english1234/vstcm/Teensy code/vst_Colour_Mod_v3_stable/vst_Colour_Mod_v3_stable.ino

/*
   VSTCM

   Vector Signal Transceiver Colour Mod using MCP4922 DACs on the Teensy 4.1

   Based on: https://trmm.net/V.st by Trammell Hudson
   incorporating mods made by "Swapfile" (Github) for Advanced Mame compatibility
   and performance optimisations by Fred Cawthorne

   robin@robinchampion.com 2022

*/

#include "main.h"

extern bool should_quit;

void _emu_printf(char *msg) {
  Serial.println(msg);
}

void setup() {
  vstcm_setup();
}

void loop() {
  while (!should_quit)
    mainloop();
}
