english1234/vstcm/Teensy code/vst_Colour_Mod_v3_stable/cinemu.cpp

/*********************************************************
* CINEMU - Cinematronics Emulator / Debugger             *
*                                                        *
* by Zonn Moore 1997                                     *
*                                                        *
* Adapted for Teensy 4.1 / VSTCM colour vector generator *
* Robin Champion September 2022                          *
* robin@robinchampion.com                                *
*                                                        *
**********************************************************/

#include "main.h"

#ifdef VSTCM

#include <arduino.h>
#include <Bounce2.h>
#include <SD.h>

#else

#pragma warning(disable : 4996)  // Get rid of annoying compiler warnings in VC++
#include <cstdio>
#include <cstring>
#include <vcruntime_string.h>
#include <random>
#include SDL_PATH

#endif

#include "cinemu.h"
#include "drawing.h"

#ifdef VSTCM
// Bounce objects to read five pushbuttons (pins 0-4)
static Bounce button0 = Bounce();
static Bounce button1 = Bounce();
static Bounce button2 = Bounce();
static Bounce button3 = Bounce();
static Bounce button4 = Bounce();

extern void SPI_flush();
#else
extern SDL_Renderer *rend_2D_orig;  // Renderer for original 2D game
#endif

UINT8 *rom;  // Allocated as 0x8000 by a malloc
extern char gMsg[50];

/* Simple public domain implementation of the standard CRC32 checksum.
 * Outputs the checksum for each file given as a command line argument.
 * Invalid file names and files that cause errors are silently skipped.
 * The program reads from stdin if it is called with no arguments. */

uint32_t crc32_for_byte(uint32_t r) {
  for (int j = 0; j < 8; ++j)
    r = (r & 1 ? 0 : (uint32_t)0xEDB88320L) ^ r >> 1;
  return r ^ (uint32_t)0xFF000000L;
}

uint32_t crc32(const void *data, size_t n_bytes, uint32_t *crc) {
  static uint32_t table[0x100];
  if (!*table)
    for (size_t i = 0; i < 0x100; ++i)
      table[i] = crc32_for_byte(i);

  for (size_t i = 0; i < n_bytes; ++i)
    *crc = table[(uint8_t)*crc ^ ((uint8_t *)data)[i]] ^ *crc >> 8;
  return *crc;
}

int loadROM(const char *fn, unsigned char *block, const unsigned len) {
#ifdef VSTCM
  unsigned j;

  // open the file on the sd card
  File dataFile = SD.open(fn, FILE_READ);

  if (dataFile) {
    //Serial.println(fn);

    for (j = 0; j < len; j++)
      block[j] = dataFile.read();

    // close the file:
    dataFile.close();

    return 0;
  }

  // if the file didn't open, print an error:
  //Serial.print("Error opening file: ");
  //Serial.println(fn);
#else
  char rompath[100];
  strcpy(rompath, MY_ROMPATH);
  strcat(rompath, fn);

  FILE *f = fopen(rompath, "rb");
  if (f == NULL) {
    strcpy(gMsg, "error: can't open file");
    fprintf(stderr, "error: can't open file '%s'.\n", rompath);
    return 1;
  }

  size_t result = fread(block, sizeof(uint8_t), len, f);
  if (result != len) {
    strcpy(gMsg, "error: while reading file");
    fprintf(stderr, "error: while reading file '%s'\n", rompath);
    return 1;
  }

  fclose(f);
  return 0;
#endif
  return -1;
}

/**************************** main **********************************/
int Game;

#define No 0
#define Yes 1

bool loadTailgunner() {
  //Serial.println("loadTailgunner: starting");
  unsigned char romLoad[0x2000];
  int r = 0;
  r += loadROM("roms/tailg/tgunner.t70", &romLoad[0x0000], 0x800);
  r += loadROM("roms/tailg/tgunner.p70", &romLoad[0x0800], 0x800);
  r += loadROM("roms/tailg/tgunner.t71", &romLoad[0x1000], 0x800);
  r += loadROM("roms/tailg/tgunner.p71", &romLoad[0x1800], 0x800);
  uint32_t crc;

  crc = 0;
  if (crc32(&romLoad[0x0000], 0x800, &crc) != 0x21EC9A04) r -= 1;
  crc = 0;
  if (crc32(&romLoad[0x0800], 0x800, &crc) != 0x8D7410B3) r -= 1;
  crc = 0;
  if (crc32(&romLoad[0x1000], 0x800, &crc) != 0x2C954AB6) r -= 1;
  crc = 0;
  if (crc32(&romLoad[0x1800], 0x800, &crc) != 0x8E2C8494) r -= 1;

  for (int i = 0; i < 0x800; i++) {
    rom[i * 2] = romLoad[0x0000 + i];
    rom[1 + i * 2] = romLoad[0x0800 + i];
    rom[0x1000 + i * 2] = romLoad[0x1000 + 0x0000 + i];
    rom[0x1000 + 1 + i * 2] = romLoad[0x1000 + 0x0800 + i];
  }

  if (r != 0) {
    strcpy(gMsg, "TROUBLE WITH TAIL GUNNER ROMS!");
    //Serial.println("TROUBLE WITH TAIL GUNNER ROMS!");
    return false;
  }

  return true;
}

bool loadRipoff() {
  unsigned char romLoad[0x2000];
  int r = 0;
  r += loadROM("roms/ripoff/ripoff.t7", &romLoad[0x0000], 0x800);
  r += loadROM("roms/ripoff/ripoff.p7", &romLoad[0x0800], 0x800);
  r += loadROM("roms/ripoff/ripoff.u7", &romLoad[0x1000], 0x800);
  r += loadROM("roms/ripoff/ripoff.r7", &romLoad[0x1800], 0x800);
  uint32_t crc;

  crc = 0;
  if (crc32(&romLoad[0x0000], 0x800, &crc) != 0x40C2C5B8) r -= 1;
  crc = 0;
  if (crc32(&romLoad[0x0800], 0x800, &crc) != 0xA9208AFB) r -= 1;
  crc = 0;
  if (crc32(&romLoad[0x1000], 0x800, &crc) != 0x29C13701) r -= 1;
  crc = 0;
  if (crc32(&romLoad[0x1800], 0x800, &crc) != 0x150BD4C8) r -= 1;

  for (int i = 0; i < 0x800; i++) {
    rom[i * 2] = romLoad[0x0000 + i];
    rom[1 + i * 2] = romLoad[0x0800 + i];
    rom[0x1000 + i * 2] = romLoad[0x1000 + 0x0000 + i];
    rom[0x1000 + 1 + i * 2] = romLoad[0x1000 + 0x0800 + i];
  }

  if (r != 0) {
    strcpy(gMsg, "TROUBLE WITH RIP OFF ROMS!");
    //Serial.println("TROUBLE WITH RIP OFF ROMS!");
    return false;
  }

  return true;
}

bool loadArmorAttack() {
  unsigned char romLoad[0x4000];
  int r = 0;
  r += loadROM("roms/armora/ar414le.t6", &romLoad[0x0000], 0x800);
  r += loadROM("roms/armora/ar414lo.p6", &romLoad[0x1000], 0x800);
  r += loadROM("roms/armora/ar414ue.u6", &romLoad[0x2000], 0x800);
  r += loadROM("roms/armora/ar414uo.r6", &romLoad[0x3000], 0x800);
  uint32_t crc;

  crc = 0;
  if (crc32(&romLoad[0x0000], 0x1000, &crc) != 0xD7E71F84) r -= 1;
  crc = 0;
  if (crc32(&romLoad[0x1000], 0x1000, &crc) != 0xDF1C2370) r -= 1;
  crc = 0;
  if (crc32(&romLoad[0x2000], 0x1000, &crc) != 0xB0276118) r -= 1;
  crc = 0;
  if (crc32(&romLoad[0x3000], 0x1000, &crc) != 0x229D779F) r -= 1;

  for (int i = 0; i < 0x1000; i++) {
    rom[i * 2] = romLoad[0x0000 + i];
    rom[1 + i * 2] = romLoad[0x1000 + i];
    rom[0x2000 + i * 2] = romLoad[0x2000 + 0x0000 + i];
    rom[0x2000 + 1 + i * 2] = romLoad[0x2000 + 0x1000 + i];
  }

  if (r != 0) {
    strcpy(gMsg, "TROUBLE WITH ARMOR ATTACK ROMS!");
    //Serial.println("TROUBLE WITH ARMOR ATTACK ROMS!");
    return false;
  }

  return true;
}

bool loadDemon() {
  unsigned char romLoad[0x4000];
  int r = 0;
  r += loadROM("roms/demon/demon.7t", &romLoad[0x0000], 0x800);
  r += loadROM("roms/demon/demon.7p", &romLoad[0x1000], 0x800);
  r += loadROM("roms/demon/demon.7u", &romLoad[0x2000], 0x800);
  r += loadROM("roms/demon/demon.7r", &romLoad[0x3000], 0x800);
  uint32_t crc;

  crc = 0;
  if (crc32(&romLoad[0x0000], 0x1000, &crc) != 0x866596C1) r -= 1;
  crc = 0;
  if (crc32(&romLoad[0x1000], 0x1000, &crc) != 0x1109E2F1) r -= 1;
  crc = 0;
  if (crc32(&romLoad[0x2000], 0x1000, &crc) != 0xD447A3C3) r -= 1;
  crc = 0;
  if (crc32(&romLoad[0x3000], 0x1000, &crc) != 0x64B515F0) r -= 1;

  for (int i = 0; i < 0x1000; i++) {
    rom[i * 2] = romLoad[0x0000 + i];
    rom[1 + i * 2] = romLoad[0x1000 + i];
    rom[0x2000 + i * 2] = romLoad[0x2000 + 0x0000 + i];
    rom[0x2000 + 1 + i * 2] = romLoad[0x2000 + 0x1000 + i];
  }

  if (r != 0) {
    strcpy(gMsg, "TROUBLE WITH DEMON ROMS!");
    //Serial.println("TROUBLE WITH DEMON ROMS!");
    return false;
  }

  return true;
}

bool loadSolarQuest() {
  unsigned char romLoad[0x4000];
  int r = 0;
  uint32_t crc;

  r += loadROM("roms/solarq/solar.6t", &romLoad[0x0000], 0x800);
  r += loadROM("roms/solarq/solar.6p", &romLoad[0x1000], 0x800);
  r += loadROM("roms/solarq/solar.6u", &romLoad[0x2000], 0x800);
  r += loadROM("roms/solarq/solar.6r", &romLoad[0x3000], 0x800);
  if (r == 0) {

  } else {
    r = 0;
    r += loadROM("roms/solarq/sq-2_le.6t", &romLoad[0x0000], 0x1000);
    r += loadROM("roms/solarq/sq-2_lo.6p", &romLoad[0x1000], 0x1000);
    r += loadROM("roms/solarq/sq-2_ue.6u", &romLoad[0x2000], 0x1000);
    r += loadROM("roms/solarq/sq-2_uo.6r", &romLoad[0x3000], 0x1000);
  }

  crc = 0;
  if (crc32(&romLoad[0x0000], 0x1000, &crc) != 0x1F3C5333) r -= 1;
  crc = 0;
  if (crc32(&romLoad[0x1000], 0x1000, &crc) != 0xD6C16BCC) r -= 1;
  crc = 0;
  if (crc32(&romLoad[0x2000], 0x1000, &crc) != 0xA5970E5C) r -= 1;
  crc = 0;
  if (crc32(&romLoad[0x3000], 0x1000, &crc) != 0xB763FFF2) r -= 1;

  for (int i = 0; i < 0x1000; i++) {
    rom[i * 2] = romLoad[0x0000 + i];
    rom[1 + i * 2] = romLoad[0x1000 + i];
    rom[0x2000 + i * 2] = romLoad[0x2000 + 0x0000 + i];
    rom[0x2000 + 1 + i * 2] = romLoad[0x2000 + 0x1000 + i];
  }

  if (r != 0) {
    strcpy(gMsg, "TROUBLE WITH SOLAR QUEST ROMS!");
    //Serial.println("TROUBLE WITH SOLAR QUEST ROMS!");
    return false;
  }

  return true;
}

bool loadWotw() {
  unsigned char romLoad[0x4000];
  int r = 0;
  r += loadROM("roms/wotw/wow_le.t7", &romLoad[0x0000], 0x1000);
  r += loadROM("roms/wotw/wow_lo.p7", &romLoad[0x1000], 0x1000);
  r += loadROM("roms/wotw/wow_ue.u7", &romLoad[0x2000], 0x1000);
  r += loadROM("roms/wotw/wow_uo.r7", &romLoad[0x3000], 0x1000);
  uint32_t crc;

  crc = 0;
  if (crc32(&romLoad[0x0000], 0x1000, &crc) != 0xB16440F9) r -= 1;
  crc = 0;
  if (crc32(&romLoad[0x1000], 0x1000, &crc) != 0xBFDF4A5A) r -= 1;
  crc = 0;
  if (crc32(&romLoad[0x2000], 0x1000, &crc) != 0x9B5CEA48) r -= 1;
  crc = 0;
  if (crc32(&romLoad[0x3000], 0x1000, &crc) != 0xC9D3C866) r -= 1;

  for (int i = 0; i < 0x1000; i++) {
    rom[i * 2] = romLoad[0x0000 + i];
    rom[1 + i * 2] = romLoad[0x1000 + i];
    rom[0x2000 + i * 2] = romLoad[0x2000 + 0x0000 + i];
    rom[0x2000 + 1 + i * 2] = romLoad[0x2000 + 0x1000 + i];
  }

  if (r != 0) {
    strcpy(gMsg, "TROUBLE WITH WAR OF THE WORLDS ROMS!");
    //Serial.println("TROUBLE WITH WAR OF THE WORLDS ROMS!");
    return false;
  }

  return true;
}

bool loadStarCastle() {
  unsigned char romLoad[0x4000];
  int r = 0;
  r += loadROM("roms/starcas/starcas3.t7", &romLoad[0x0000], 0x0800);
  r += loadROM("roms/starcas/starcas3.p7", &romLoad[0x0800], 0x0800);
  r += loadROM("roms/starcas/starcas3.u7", &romLoad[0x1000], 0x0800);
  r += loadROM("roms/starcas/starcas3.r7", &romLoad[0x1800], 0x0800);
  uint32_t crc;

  crc = 0;
  if (crc32(&romLoad[0x0000], 0x0800, &crc) != 0xB5838B5D) r -= 1;
  crc = 0;
  if (crc32(&romLoad[0x0800], 0x0800, &crc) != 0xF6BC2F4D) r -= 1;
  crc = 0;
  if (crc32(&romLoad[0x1000], 0x0800, &crc) != 0x188CD97C) r -= 1;
  crc = 0;
  if (crc32(&romLoad[0x1800], 0x0800, &crc) != 0xC367B69D) r -= 1;

  for (int i = 0; i < 0x0800; i++) {
    rom[i * 2] = romLoad[0x0000 + i];
    rom[1 + i * 2] = romLoad[0x0800 + i];
    rom[0x1000 + i * 2] = romLoad[0x1000 + 0x0000 + i];
    rom[0x1000 + 1 + i * 2] = romLoad[0x1000 + 0x0800 + i];
  }

  if (r != 0) {
    strcpy(gMsg, "TROUBLE WITH STAR CASTLE ROMS!");
    //Serial.println("TROUBLE WITH STAR CASTLE ROMS!");
    return false;
  }

  return true;
}

bool loadSpeedFreak() {
  unsigned char romLoad[0x4000];
  int r = 0;
  r += loadROM("roms/speedfrk/speedfrk.t7", &romLoad[0x0000], 0x0800);
  r += loadROM("roms/speedfrk/speedfrk.p7", &romLoad[0x0800], 0x0800);
  r += loadROM("roms/speedfrk/speedfrk.u7", &romLoad[0x1000], 0x0800);
  r += loadROM("roms/speedfrk/speedfrk.r7", &romLoad[0x1800], 0x0800);
  uint32_t crc;

  crc = 0;
  if (crc32(&romLoad[0x0000], 0x0800, &crc) != 0x3552C03F) r -= 1;
  crc = 0;
  if (crc32(&romLoad[0x0800], 0x0800, &crc) != 0x4B90CDEC) r -= 1;
  crc = 0;
  if (crc32(&romLoad[0x1000], 0x0800, &crc) != 0x616C7CF9) r -= 1;
  crc = 0;
  if (crc32(&romLoad[0x1800], 0x0800, &crc) != 0xFBE90D63) r -= 1;

  for (int i = 0; i < 0x0800; i++) {
    rom[i * 2] = romLoad[0x0000 + i];
    rom[1 + i * 2] = romLoad[0x0800 + i];
    rom[0x1000 + i * 2] = romLoad[0x1000 + 0x0000 + i];
    rom[0x1000 + 1 + i * 2] = romLoad[0x1000 + 0x0800 + i];
  }

  if (r != 0) {
    strcpy(gMsg, "TROUBLE WITH SPEED FREAK ROMS!");
    //Serial.println("TROUBLE WITH SPEED FREAK ROMS!");
    return false;
  }

  return true;
}

bool loadWarrior() {
  unsigned char romLoad[0x4000];
  int r = 0;
  r += loadROM("roms/warrior/warrior.t7", &romLoad[0x0000], 0x0800);
  r += loadROM("roms/warrior/warrior.p7", &romLoad[0x0800], 0x0800);
  r += loadROM("roms/warrior/warrior.u7", &romLoad[0x1000], 0x0800);
  r += loadROM("roms/warrior/warrior.r7", &romLoad[0x1800], 0x0800);
  uint32_t crc;

  crc = 0;
  if (crc32(&romLoad[0x0000], 0x0800, &crc) != 0xAC3646F9) r -= 1;
  crc = 0;
  if (crc32(&romLoad[0x0800], 0x0800, &crc) != 0x517D3021) r -= 1;
  crc = 0;
  if (crc32(&romLoad[0x1000], 0x0800, &crc) != 0x2E39340F) r -= 1;
  crc = 0;
  if (crc32(&romLoad[0x1800], 0x0800, &crc) != 0x8E91B502) r -= 1;

  for (int i = 0; i < 0x0800; i++) {
    rom[i * 2] = romLoad[0x0000 + i];
    rom[1 + i * 2] = romLoad[0x0800 + i];
    rom[0x1000 + i * 2] = romLoad[0x1000 + 0x0000 + i];
    rom[0x1000 + 1 + i * 2] = romLoad[0x1000 + 0x0800 + i];
  }

  if (r != 0) {
    strcpy(gMsg, "TROUBLE WITH WARRIOR ROMS!");
    //Serial.println("TROUBLE WITH WARRIOR ROMS!");
    return false;
  }

  return true;
}

bool loadSundance() {
  unsigned char romLoad[0x4000];
  int r = 0;
  r += loadROM("roms/sundance/sundance.t7", &romLoad[0x0000], 0x0800);
  r += loadROM("roms/sundance/sundance.p7", &romLoad[0x0800], 0x0800);
  r += loadROM("roms/sundance/sundance.u7", &romLoad[0x1000], 0x0800);
  r += loadROM("roms/sundance/sundance.r7", &romLoad[0x1800], 0x0800);
  uint32_t crc;

  crc = 0;
  if (crc32(&romLoad[0x0000], 0x0800, &crc) != 0xD5B9CB19) r -= 1;
  crc = 0;
  if (crc32(&romLoad[0x0800], 0x0800, &crc) != 0x445C4F20) r -= 1;
  crc = 0;
  if (crc32(&romLoad[0x1000], 0x0800, &crc) != 0x67887D48) r -= 1;
  crc = 0;
  if (crc32(&romLoad[0x1800], 0x0800, &crc) != 0x10B77EBD) r -= 1;

  for (int i = 0; i < 0x0800; i++) {
    rom[i * 2] = romLoad[0x0000 + i];
    rom[1 + i * 2] = romLoad[0x0800 + i];
    rom[0x1000 + i * 2] = romLoad[0x1000 + 0x0000 + i];
    rom[0x1000 + 1 + i * 2] = romLoad[0x1000 + 0x0800 + i];
  }

  if (r != 0) {
    strcpy(gMsg, "TROUBLE WITH SUNDANCE ROMS!");
    //Serial.println("TROUBLE WITH SUNDANCE ROMS!");
    return false;
  }

  return true;
}

bool loadSpaceWar() {
  unsigned char romLoad[0x2000];
  int r = 0;
  r += loadROM("roms/spacewar/spacewar.1l", &romLoad[0x0000], 0x0800);
  r += loadROM("roms/spacewar/spacewar.2r", &romLoad[0x0800], 0x0800);
  uint32_t crc;

  crc = 0;
  if (crc32(&romLoad[0x0000], 0x800, &crc) != 0xEDF0FD53) r -= 1;
  crc = 0;
  if (crc32(&romLoad[0x0800], 0x800, &crc) != 0x4F21328B) r -= 1;

  for (int i = 0; i < 0x800; i++) {
    rom[i * 2] = romLoad[0x0000 + i];
    rom[1 + i * 2] = romLoad[0x0800 + i];
  }


  if (r != 0) {
    strcpy(gMsg, "TROUBLE WITH SPACE WARS ROMS!");
    //Serial.println("TROUBLE WITH SPACE WARS ROMS!");
    return false;
  }

  return true;
}

bool loadStarHawk() {
  unsigned char romLoad[0x2000];
  int r = 0;
  r += loadROM("roms/starhawk/u7", &romLoad[0x0000], 0x0800);
  r += loadROM("roms/starhawk/r7", &romLoad[0x0800], 0x0800);
  uint32_t crc;
  crc = 0;

  crc = 0;
  if (crc32(&romLoad[0x0000], 0x800, &crc) != 0x376E6C5C) r -= 1;
  crc = 0;
  if (crc32(&romLoad[0x0800], 0x800, &crc) != 0xBB71144F) r -= 1;

  for (int i = 0; i < 0x800; i++) {
    rom[i * 2] = romLoad[0x0000 + i];
    rom[1 + i * 2] = romLoad[0x0800 + i];
  }

  if (r != 0) {
    strcpy(gMsg, "TROUBLE WITH STAR HAWK ROMS!");
    //Serial.println("TROUBLE WITH STAR HAWK ROMS!");
    return false;
  }

  return true;
}

bool loadBarrier() {
  unsigned char romLoad[0x2000];
  int r = 0;
  r += loadROM("roms/barrier/barrier.t7", &romLoad[0x0000], 0x0800);
  r += loadROM("roms/barrier/barrier.p7", &romLoad[0x0800], 0x0800);
  uint32_t crc;
  crc = 0;

  crc = 0;
  if (crc32(&romLoad[0x0000], 0x800, &crc) != 0x7C3D68C8) r -= 1;
  crc = 0;
  if (crc32(&romLoad[0x0800], 0x800, &crc) != 0xAEC142B5) r -= 1;

  for (int i = 0; i < 0x800; i++) {
    rom[i * 2] = romLoad[0x0000 + i];
    rom[1 + i * 2] = romLoad[0x0800 + i];
  }

  if (r != 0) {
    strcpy(gMsg, "TROUBLE WITH BARRIER ROMS!");
    //Serial.println("TROUBLE WITH BARRIER ROMS!");
    return false;
  }

  return true;
}

bool loadBoxingBugs() {
  unsigned char romLoad[0x8000];
  int r = 0;
  r += loadROM("roms/boxingb/u1a", &romLoad[0x0000], 0x1000);
  r += loadROM("roms/boxingb/u1b", &romLoad[0x1000], 0x1000);
  r += loadROM("roms/boxingb/u2a", &romLoad[0x2000], 0x1000);
  r += loadROM("roms/boxingb/u2b", &romLoad[0x3000], 0x1000);
  r += loadROM("roms/boxingb/u3a", &romLoad[0x4000], 0x1000);
  r += loadROM("roms/boxingb/u3b", &romLoad[0x5000], 0x1000);
  r += loadROM("roms/boxingb/u4a", &romLoad[0x6000], 0x1000);
  r += loadROM("roms/boxingb/u4b", &romLoad[0x7000], 0x1000);
  uint32_t crc;

  crc = 0;
  if (crc32(&romLoad[0x0000], 0x1000, &crc) != 0xD3115B0F) r -= 1;
  crc = 0;
  if (crc32(&romLoad[0x1000], 0x1000, &crc) != 0x3A44268D) r -= 1;
  crc = 0;
  if (crc32(&romLoad[0x2000], 0x1000, &crc) != 0xC97A9CBB) r -= 1;
  crc = 0;
  if (crc32(&romLoad[0x3000], 0x1000, &crc) != 0x98D34FF5) r -= 1;
  crc = 0;
  if (crc32(&romLoad[0x4000], 0x1000, &crc) != 0x5BB3269B) r -= 1;
  crc = 0;
  if (crc32(&romLoad[0x5000], 0x1000, &crc) != 0x85BF83AD) r -= 1;
  crc = 0;
  if (crc32(&romLoad[0x6000], 0x1000, &crc) != 0x25B51799) r -= 1;
  crc = 0;
  if (crc32(&romLoad[0x7000], 0x1000, &crc) != 0x7F41DE6A) r -= 1;

  for (int i = 0; i < 0x1000; i++) {
    rom[i * 2] = romLoad[0x0000 + i];
    rom[1 + i * 2] = romLoad[0x1000 + i];
    rom[0x2000 + i * 2] = romLoad[0x2000 + 0x0000 + i];
    rom[0x2000 + 1 + i * 2] = romLoad[0x2000 + 0x1000 + i];
    rom[0x4000 + i * 2] = romLoad[0x4000 + 0x0000 + i];
    rom[0x4000 + 1 + i * 2] = romLoad[0x4000 + 0x1000 + i];
    rom[0x6000 + i * 2] = romLoad[0x6000 + 0x0000 + i];
    rom[0x6000 + 1 + i * 2] = romLoad[0x6000 + 0x1000 + i];
  }

  if (r != 0) {
    strcpy(gMsg, "TROUBLE WITH BOXING BUGS ROMS!");
    //Serial.println("TROUBLE WITH BOXING BUGS ROMS!");
    return false;
  }

  return true;
}

bool loadCosmicChasm() {
  int r = 1;
  // this seems to be a 64k ROM
  // - or I don't know how to load it...

  // MAME roms contain u1 - u16 (each 4k)
  /*
   * 
   * Is there a bankswitch
   * Or do they use the full 64kk address space?
     RomImages[0]="roms/cosmicchasm/chasm.u4";
     RomImages[1]="roms/cosmicchasm/chasm.u12";
     RomImages[2]="roms/cosmicchasm/chasm.u8";
     RomImages[3]="roms/cosmicchasm/chasm.u16";
     RomImages[4]="roms/cosmicchasm/chasm.u3";
     RomImages[5]="roms/cosmicchasm/chasm.u11";
     RomImages[6]="roms/cosmicchasm/chasm.u7";
     RomImages[7]="roms/cosmicchasm/chasm.u15";
     
     what about 1 / 9
     what about 2 / 10
     what about 5 / 13
     what about 6 / 14
     ???
     
     INFO: MAME
     MCFG_CPU_ADD("maincpu", M68000, CCHASM_68K_CLOCK)    / * 8 MHz (from schematics) * /
     
ROM_START( cchasm )
    ROM_REGION( 0x010000, "maincpu", 0 )
    ROM_LOAD16_BYTE( "chasm.u4",  0x000000, 0x001000, CRC(19244f25) SHA1(79deaae82da8d1b16d05bbac43ba900c4b1d9f26) )
    ROM_LOAD16_BYTE( "chasm.u12", 0x000001, 0x001000, CRC(5d702c7d) SHA1(cbdceed45a1112594fbcbeb6976edc932b32d518) )
    ROM_LOAD16_BYTE( "chasm.u8",  0x002000, 0x001000, CRC(56a7ce8a) SHA1(14c790dcddb78d3b81b5a65fe3529e42c9708273) )
    ROM_LOAD16_BYTE( "chasm.u16", 0x002001, 0x001000, CRC(2e192db0) SHA1(1a8ff983295ab52b5099c089b3142cdc56d28aee) )
    ROM_LOAD16_BYTE( "chasm.u3",  0x004000, 0x001000, CRC(9c71c600) SHA1(900526eaff7483fc478ebfb3f14796ff8fd1d01f) )
    ROM_LOAD16_BYTE( "chasm.u11", 0x004001, 0x001000, CRC(a4eb59a5) SHA1(a7bb3ca8f1f000f224def6342ca9d1eabcb210e6) )
    ROM_LOAD16_BYTE( "chasm.u7",  0x006000, 0x001000, CRC(8308dd6e) SHA1(82ad7c27e9a41af5280ecd975d3530ff2ed27ad4) )
    ROM_LOAD16_BYTE( "chasm.u15", 0x006001, 0x001000, CRC(9d3abf97) SHA1(476d684182d92d66263df82e1b5c4ff24b6814e8) )
    ROM_LOAD16_BYTE( "u2",        0x008000, 0x001000, CRC(4e076ae7) SHA1(a72f5425b256785b810ee5f23917b44f778cfcd3) )
    ROM_LOAD16_BYTE( "u10",       0x008001, 0x001000, CRC(cc9e19ca) SHA1(6c46ec265c2cc0683470ed1df978b96b577c5ca1) )
    ROM_LOAD16_BYTE( "chasm.u6",  0x00a000, 0x001000, CRC(a96525d2) SHA1(1c41bc3bf051cf1830182cbde6fba4e56db7e431) )
    ROM_LOAD16_BYTE( "chasm.u14", 0x00a001, 0x001000, CRC(8e426628) SHA1(2d70a7717b18cc892332b9d5d2de3ceba6c1481d) )
    ROM_LOAD16_BYTE( "u1",        0x00c000, 0x001000, CRC(88b71027) SHA1(49fa676d7838c643d642fbc70579ce29e76ba724) )
    ROM_LOAD16_BYTE( "chasm.u9",  0x00c001, 0x001000, CRC(d90c9773) SHA1(4033f0579f0782db2157f6cbece53b0d74e61d4f) )
    ROM_LOAD16_BYTE( "chasm.u5",  0x00e000, 0x001000, CRC(e4a58b7d) SHA1(0e5f948cd110804e6119fafb4e3fa5904dd1390f) )
    ROM_LOAD16_BYTE( "chasm.u13", 0x00e001, 0x001000, CRC(877e849c) SHA1(bdeb97fcb7488e7f0866dd651204c362d2ec9f4f) )

    ROM_REGION( 0x10000, "audiocpu", 0 )
    ROM_LOAD( "2732.bin", 0x0000, 0x1000, CRC(715adc4a) SHA1(426be4f3334ef7f2e8eb4d533e64276c30812aa3) )

    ROM_REGION( 0x0200, "plds", 0 )
    ROM_LOAD( "pal12l6.u76", 0x0000, 0x0034, CRC(a30e02b7) SHA1(572f6d3f03e559f12e3bd5e087d7680ac69e9182) )
    ROM_LOAD( "pal12l6.u77", 0x0100, 0x0034, CRC(458b9cdb) SHA1(a3bff56d805f6dc494d294f079c3580430acf317) )
ROM_END     
     
     */
  if (r != 0) {
    strcpy(gMsg, "TROUBLE WITH COSMIC CHASM ROMS!");
    //Serial.println("TROUBLE WITH COSMIC CHASM ROMS!");
    return false;
  }

  return true;
}

bool loadQB3() {
  unsigned char romLoad[0x8000];
  int r = 0;

  r += loadROM("roms/qb3/qb3_le_t7.bin", &romLoad[0x0000], 0x2000);
  r += loadROM("roms/qb3/qb3_lo_p7.bin", &romLoad[0x2000], 0x2000);
  r += loadROM("roms/qb3/qb3_ue_u7.bin", &romLoad[0x4000], 0x2000);
  r += loadROM("roms/qb3/qb3_uo_r7.bin", &romLoad[0x6000], 0x2000);

  uint32_t crc;

  crc = 0;
  if (crc32(&romLoad[0x0000], 0x2000, &crc) != 0xADAAEE4C) r -= 1;
  crc = 0;
  if (crc32(&romLoad[0x2000], 0x2000, &crc) != 0x72F6199F) r -= 1;
  crc = 0;
  if (crc32(&romLoad[0x4000], 0x2000, &crc) != 0x050A996D) r -= 1;
  crc = 0;
  if (crc32(&romLoad[0x6000], 0x2000, &crc) != 0x33FA77A2) r -= 1;

  for (int i = 0; i < 0x2000; i++) {
    rom[i * 2] = romLoad[0x0000 + i];
    rom[1 + i * 2] = romLoad[0x2000 + i];
    rom[0x4000 + i * 2] = romLoad[0x4000 + 0x0000 + i];
    rom[0x4000 + 1 + i * 2] = romLoad[0x4000 + 0x2000 + i];
  }

  if (r != 0) {
    strcpy(gMsg, "TROUBLE WITH QB3 ROMS!");
    //Serial.println("TROUBLE WITH QB3 ROMS!");
    return false;
  }

  return true;
}

// these should be in the vectrex library
#define VEC_BUTTON_1_1 0x01
#define VEC_BUTTON_1_2 0x02
#define VEC_BUTTON_1_3 0x04
#define VEC_BUTTON_1_4 0x08
#define VEC_BUTTON_2_1 0x10
#define VEC_BUTTON_2_2 0x20
#define VEC_BUTTON_2_3 0x40
#define VEC_BUTTON_2_4 0x80

// Put any switch or IO bits that are common to all machines here.
#define SW_ABORT 0x100 /* for ioSwitches */

int useParity = 0;

static int world_xl = -1800, world_yb = -2400, world_xr = 1800, world_yt = 2400;  // dummy values should never be used

unsigned long isqrt(unsigned long x) {
  unsigned long op, res, one;

  op = x;
  res = 0;

  /* "one" starts at the highest power of four <= than the argument. */
  one = 1 << 30; /* second-to-top bit set */
  while (one > op) one >>= 2;

  while (one != 0) {
    if (op >= res + one) {
      op -= res + one;
      res += one << 1;  // <-- faster than 2 * one
    }
    res >>= 1;
    one >>= 2;
  }
  return res;
}

const int /*fp14*/ sine[] = {
  0,
  402,
  803,
  1205,
  1605,
  2005,
  2404,
  2801,
  3196,
  3589,
  3980,
  4369,
  4756,
  5139,
  5519,
  5896,
  6269,
  6639,
  7005,
  7366,
  7723,
  8075,
  8423,
  8765,
  9102,
  9434,
  9759,
  10079,
  10393,
  10701,
  11002,
  11297,
  11585,
  11866,
  12139,
  12406,
  12665,
  12916,
  13159,
  13395,
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
};

FILE *debugf = NULL;

#define DEBUG_OUT(a, b) \
  Serial.print(a); \
  Serial.print(" "); \
  Serial.println(b);

/*#ifndef false
#define false (0 != 0)
#define true (0 == 0)
#endif*/

// Start of CCPU emulator

int ccpudebug = 0; /* default is off (0) - can be turned on with -d flag */

// war of the worlds had a missing instruction.  Now added and it runs.

/*
boxingbugs had a missing instruction:

2EAE: C8    : ldi  $8     : A=047 B=045 I=047Z J=E9B P=1 A0=46 00 N1 O46 A
2EAF: EA    : lda  [i]    : A=18D B=045 I=047Z J=E9B P=1 A0=47 00 N18D O47 AA
2EB0: D7    : sta  $7     : A=18D B=045 I=017Z J=E9B P=1 A0=47 00 N18D O47 A
2EB1: 02    : lda  #$200  : A=200 B=045 I=017Z J=E9B P=1 A0=8D 01 N200 O18D AA
2EB2: 76    : sub  $6     : A=13C B=045 I=016Z J=E9B P=1 A0=00 11 NC4 O200 AA
2EB3: 57    : nopb        : A=13C B=045 I=016Z J=E9B P=1 A0=00 11 NC4 O200   B
2EB4: 03    : lda  #$300  : A=13C B=300 I=016Z J=E9B P=1 A0=3C 01 N300 O45 AA
2EB5: 57    : nopb        : A=13C B=300 I=016Z J=E9B P=1 A0=3C 01 N300 O45   B
2eb6 DANGER: Unimplemented instruction - opLSRe B 1
 */

/*

Had to add missing opcode to get cosmicchasm to run - now it runs but is
stuck in a loop:

0840: 30 39 : sub  #$39   : A=040 B=039 I=08CZ J=840 P=8 A0=40 10 N39 O72 AA
0842: 00    : clr         : A=000 B=039 I=08CZ J=840 P=8 A0=40 00 N0 O40 AA
0843: FF    : lsld        : A=000 B=072 I=08CZ J=840 P=8 A0=00 0F NFFF O0 AA
0844: EA    : lda  [i]    : A=000 B=072 I=08CZ J=840 P=8 A0=00 00 N0 O0 AA
0845: 90    : out  $0     : A=000 B=072 I=08CZ J=840 P=8 A0=00 00 N0 O0 A
0846: E3    : mul  [i]    : A=000 B=039 I=08CZ J=840 P=8 A0=00 00 N0 O0 AA
0847: 40 48 : ldj  #$840  : A=000 B=039 I=08CZ J=840 P=8 A0=00 00 N0 O0 A
0849: C0    : ldi  $0     : A=000 B=039 I=000Z J=840 P=8 A0=00 00 N0 O0 A
084A: D0    : sta  $0     : A=000 B=039 I=080Z J=840 P=8 A0=00 00 N0 O0 A
084B: BC    : cmp  $C     : A=000 B=039 I=08CZ J=840 P=8 A0=00 10 N0 O0 AA
084C: 00    : clr         : A=000 B=039 I=08CZ J=840 P=8 A0=00 00 N0 O0 AA
084D: FF    : lsld        : A=000 B=072 I=08CZ J=840 P=8 A0=00 0F NFFF O0 AA
084E: EB    : lsr         : A=000 B=072 I=08CZ J=840 P=8 A0=00 0B NBEB O0 AA
084F: 88    : ldp  #$8    : A=000 B=072 I=08CZ J=840 P=8 A0=00 0B NBEB O0 A
0850: 20 40 : add  #$40   : A=040 B=072 I=08CZ J=840 P=8 A0=00 00 N40 O0 AA
0852: 52    : jdrb <jump> : A=040 B=072 I=08CZ J=840 P=8 A0=00 00 N40 O0   B
0852: 52    : jdrb <jump> : A=040 B=072 I=08CZ J=840 P=8 A0=00 00 N40 O0   BB
0853: 50    : jppb <jump> : A=040 B=072 I=08CZ J=840 P=8 A0=00 00 N40 O0   B

*/
#define CARRYBIT (1 << 12)
#define A0BIT 1

/* Contorted sign-extend macro only evaluates its parameter once, and
   executes in two shifts.  This is far more efficient that any other
   sign extend procedure I can think of, and relatively safe */

#define SEX(twelvebit) ((((int)twelvebit) << (int)((sizeof(int) * 8) - 12)) \
                        >> (int)((sizeof(int) * 8) - 12))

/* Mouse values currently sampled once per frame and set in WAI code.
   This is not ideal. */

/* RCstate setting macros to exit opcode handler */
#define jumpCineRet_A \
  do { \
    RCstate = RCstate_A; \
    goto cineExecBottom; \
  } while (0)
#define jumpCineRet_B \
  do { \
    RCstate = RCstate_B; \
    goto cineExecBottom; \
  } while (0)
#define jumpCineRet_AA \
  do { \
    RCstate = RCstate_AA; \
    goto cineExecBottom; \
  } while (0)
#define jumpCineRet_BB \
  do { \
    RCstate = RCstate_BB; \
    goto cineExecBottom; \
  } while (0)
#define jumpCineRet_WEIRD \
  do (DEBUG_OUT( "Didn't bother yet.\n" ); exit ( 0 ); \
  } \
  while (0)

/* Handy new operators ... */

/* for Zonn translation :) */
#define SAR16(var, arg) (((signed short int)var) >> arg)

/* for setting/checking the A0 flag */
#define SETA0(var) (RCacc_a0 = var)
#define GETA0() (RCacc_a0)

/* for setting/checking the Carry flag */
#define SETFC(val) (RCflag_C = val)
#define GETFC() ((RCflag_C >> 8) & 0xFF)

/* Define new types for the c-cpu emulator */
typedef short unsigned int RCCINEWORD; /* 12bits on the C-CPU */
typedef unsigned char RCCINEBYTE;      /* 8 (or less) bits on the C-CPU */
typedef short signed int RCCINESWORD;  /* 12bits on the C-CPU */
typedef signed char RCCINESBYTE;       /* 8 (or less) bits on the C-CPU */

typedef enum {
  RCstate_A = 0,
  RCstate_AA,
  RCstate_B,
  RCstate_BB
} RCCINESTATE; /* current RCstate */

volatile static UINT32 dwElapsedTicks = 0;
static UINT8 bBailOut = false;

/* C-CPU context information begins -- */
RCCINEWORD RCregister_PC = 0; /* C-CPU registers; program counter */
RCCINEWORD RCregister_A = 0;  /* ; A-Register (accumulator) */
RCCINEWORD RCregister_B = 0;  /* ; B-Register (accumulator) */
RCCINEBYTE RCregister_I = 0;  /* ; I-Register (last access RAM location) */
RCCINEWORD RCregister_J = 0;  /* ; J-Register (target address for JMP
				   opcodes) */
RCCINEBYTE RCregister_P = 0;  /* ; Page-Register (4 bits) */
RCCINEWORD RCFromX = 0;       /* ; X-Register (start of a vector) */
RCCINEWORD RCFromY = 0;       /* ; Y-Register (start of a vector) */
RCCINEWORD RCregister_T = 0;  /* ; T-Register (vector draw length timer) */
RCCINEWORD RCflag_C = 0;      /* C-CPU flags; carry. Is word sized, instead
				   of RCCINEBYTE, so we can do direct
				   assignment and then change to BYTE during
				   inspection. */

RCCINEWORD RCcmp_old = 0; /* last accumulator value */
RCCINEWORD RCcmp_new = 0; /* new accumulator value */
RCCINEBYTE RCacc_a0 = 0;  /* bit0 of A-reg at last accumulator access */

RCCINESTATE RCstate = RCstate_A; /* C-CPU RCstate machine current
					   RCstate */
RCCINEWORD RCram[256];           /* C-CPU RCram (for all pages) */

//UINT8 rom[0x8000];  // = tailgunner was 0x2000 - others may be larger

static char ccpu_game_name[32]; /* canonical name we now use as cinemu
				   parameter */
static int ccpu_game_id = 0;    /* as set by cineSetGame */
static UINT8 ccpu_jmi_dip = 1;  /* as set by cineSetJMI */
static UINT8 ccpu_msize = 0;    /* as set by cineSetMSize */
static UINT8 ccpu_monitor = 0;  /* as set by cineSetMonitor */

/* cinem graphics junk */
RCCINEBYTE RCvgShiftLength = 0; /* number of shifts loaded into length reg */

/* -- Context information ends. */

UINT8 bFlipX;
UINT8 bFlipY;
UINT8 bSwapXY;
UINT8 bOverlay;

UINT16 ioSwitches = 0xFF;      /* high values for non-triggered switches */
UINT16 initialSwitches = 0xFF; /* high values for non-triggered switches */
UINT16 ioInputs = 0;
UINT16 initialInputs = 0;
UINT8 ioOutputs = 0;

UINT16 RCvgColour = 0;

INT16 JoyX;
INT16 JoyY;
UINT8 bNewFrame;

INT32 sdwGameXSize;
INT32 sdwGameYSize;
INT32 sdwXOffset = 0;
INT32 sdwYOffset = 0;

// This will move to the vectrex graphics library.
static int64_t ScaleXMul = 1LL, ScaleXDiv = 1LL, ScaleXOffsetPre = 0LL, ScaleXOffsetPost = 0LL,
               ScaleYMul = 1LL, ScaleYDiv = 1LL, ScaleYOffsetPre = 0LL, ScaleYOffsetPost = 0LL;
static int v_rotate = 0, v_flip_x = 0, v_flip_y = 0;
static int v_xl = 0, v_yb = 0, v_xr = 0, v_yt = 0;

int tx(int x) {  // convert x from window to viewport
  if (v_flip_x) x = v_xr - (x - v_xl);
  return (int)(((((int64_t)x) + ScaleXOffsetPre) * ScaleXMul) / ScaleXDiv + ScaleXOffsetPost);
}

int ty(int y) {  // and y
  if (v_flip_y) y = v_yt - (y - v_yb);
  return (int)(((((int64_t)y) + ScaleYOffsetPre) * ScaleYMul) / ScaleYDiv + ScaleYOffsetPost);
}

int frameCounter = 0;
static int cineTwinkle = 255;  // off by default

void line(int32_t xl, int32_t yb, int32_t xr, int32_t yt, int col) {

  /*  Serial.print("xl ");
  Serial.print(xl);
  Serial.print(" yb ");
  Serial.print(yb);
  Serial.print(" xr ");
  Serial.print(xr);
  Serial.print(" yt ");
  Serial.print(yt);
  Serial.print(" col ");
  Serial.println(col);
*/
  if (v_rotate) {
    int tmp;
    tmp = xl;
    xl = yb;
    yb = tmp;
    tmp = xr;
    xr = yt;
    yt = tmp;
    xl = v_xr - (xl - v_xl);
    xr = v_xr - (xr - v_xl);
  }

  cohen_sutherlandCustom(&xl, &yb, &xr, &yt, 128, 128, 3968, 3968);

  if (xl == 1000000)  // if not totally outside defined clipping region then draw it
    return;

  if ((ccpu_game_id == GAME_TAILGUNNER) && (xl == xr) && (yb == yt)) {
    // stars...  tweak the intensity according to the distance from the center
    int SCREEN_W = world_xr - world_xl, SCREEN_H = world_yt - world_yb;
    int dist = isqrt((SCREEN_W / 2 - xl) * (SCREEN_W / 2 - xl) + (SCREEN_H / 2 - yb) * (SCREEN_H / 2 - yb));
    int maxdist = isqrt((SCREEN_W / 2) * (SCREEN_W / 2) + (SCREEN_H / 2) * (SCREEN_H / 2));

    if (maxdist == 0)
      maxdist = 1;

    if (col == 7)
      col = (col - (((maxdist - dist) * 7) / maxdist) + 1) * 2 + 1;

    //v_directDraw32Patterned(tx(xl), ty(yb), tx(xr), ty(yt), (col + 1) * 8 - 1, random());
    //  col = (col + 1) * 8 - 1;
    // col = random(30, 160);

    draw_moveto(tx(xl), ty(yb));
    draw_to_xyrgb(tx(xr), ty(yt), col, col, col);
  } else if ((ccpu_game_id == GAME_TAILGUNNER) && (RCregister_PC == 0x03B2)) {
    // 0x1BBD - PUSH START
    // 0x03B2 - 3 lines in the shields have Twinkle values
    // Tailgunner's shields are funny and need fixing.
    //v_directDraw32Patterned(tx(xl), ty(yb), tx(xr), ty(yt), 127, random());  //one way to make sparky shields...
    //  col = random(30, 160);
    draw_moveto(tx(xl), ty(yb));
    draw_to_xyrgb(tx(xr), ty(yt), col, col, col);
    //DEBUG_OUT("line(%d,%d, %d,%d, %02x) at PC=0x%04x;\n", xl,yb, xr,yt, col, RCregister_PC);
  } else {  // All other games except Tailgunner
    /* Twinkle may be 0 (sundance), or 7-9 */
    if ((col <= cineTwinkle) || (xl != xr) || (yb != yt)) {
      // DEBUG_OUT("v_directDraw32 (%d,%d, %d,%d, %d);\n", tx(xl), ty(yb), tx(xr), ty(yt), (col + 1) * 8 - 1);
      // v_directDraw32(tx(xl), ty(yb), tx(xr), ty(yt), (col + 1) * 8 - 1);
      col = (col + 1) * 10 - 1;

    } else {  // twinkle parameter denotes flash.
      col = (127 * (sine[(frameCounter << 3) & 255] + 16384 + 32768)) / 65536;
      //  v_directDraw32(tx(xl), ty(yb), tx(xr), ty(yt), col);  // brightness 63..127
    }

    draw_moveto(tx(xl), ty(yb));
    draw_to_xyrgb(tx(xr), ty(yt), col, col, col);
  }
}

int _tx(int x) {  // convert x from window to viewport
  if (v_flip_x) x = v_xr - (x - v_xl);
  return (int)(((((int64_t)x) + ScaleXOffsetPre) * ScaleXMul) / ScaleXDiv + ScaleXOffsetPost);
}

int _ty(int y) {  // and y
  if (v_flip_y) y = v_yt - (y - v_yb);
  return (int)(((((int64_t)y) + ScaleYOffsetPre) * ScaleYMul) / ScaleYDiv + ScaleYOffsetPost);
}

void window(int xl, int yb, int xr, int yt) {
  // We will use normalised viewport coordinates of x = -18000:18000 and y = -24000:24000 for consistency
  int64_t width, height;
  int xc, yc;
  int /* oxl = xl, oyb = yb, */ oxr = xr, oyt = yt;

  v_xl = xl;
  v_yb = yb;
  v_xr = xr;
  v_yt = yt;

  width = (int64_t)xr - (int64_t)xl;
  height = (int64_t)yt - (int64_t)yb;
  // However, if OS tells us that vectrex is on its side, we'll handle these differently.
  // For now, though, Malban's orientation code is doing the rotation behind the scenes
  // so we don't want to do it twice.  Need to think about whether that solution is OK
  // or has to be changed. Although it doesn't matter too much in terms of what is displayed,
  // it makes a different with respect to loading and saving configs and using the same
  // default for multiple games.
  if (width * 4 > height * 3) {
    // window is wider than aspect ratio, so we will have black bars at the top and bottom
    // height = (width * 4) / 3;
    yc = (yb + yt) / 2;
    yb = yc - height / 2;
    yt = yc + height / 2;
  } else if (width * 4 < height * 3) {
    // window is taller than aspect ratio, so we will have black bars at
    // the sides
    width = (height * 3) / 4;
    xc = (xl + xr) / 2;
    xl = xc - width / 2;
    xr = xc + width / 2;
  }

  ScaleXMul = 4096LL;
  ScaleXDiv = width;
  // ScaleXOffsetPre = -width / 2LL;
  ScaleXOffsetPre = 0;
  ScaleXOffsetPost = 0LL;
  ScaleXOffsetPost = (tx(xr) - tx(oxr)) / 2LL;

  ScaleYMul = 4096LL;
  ScaleYDiv = height;
  // ScaleYOffsetPre = -height / 2LL;
  ScaleYOffsetPre = 0;
  ScaleYOffsetPost = 0LL;
  ScaleYOffsetPost = (ty(yt) - ty(oyt)) / 2LL;
}
// end of window library

// start of startFrame section

void startFrame_ripoff(void) {
  /*
DIP_START(ripoff_dips)
 DIP_SET4(DIPSW1,0xfc,"Units",0x00,"8",0x01,"16",0x02,"4",0x03,"12",3)
 DIP_SET4(DIPSW1,0xf3,"Coins",0x08,"2Coins 1Credit",0x00,"4Coins 3Credits",0x0c,"1Coin 1Credit",0x04,"2Coins 3Credits",2)
 DIP_SET2(DIPSW1,0xef,"Attract Sound",0x10,"Off",0x00,"On",0)
 DIP_SET2(DIPSW1,0xdf,"Scores",0x20,"Individual",0x00,"Combined",0)
 DIP_SET2(DIPSW1,0xbf,"Diagnostic",0x00,"Off",0x40,"On",0)
DIP_END
   */
#define RO_IO_P1START 0x02  // 1-player start
#define RO_IO_P1LEFT 0x1000
#define RO_IO_P1RIGHT 0x4000
#define RO_IO_P1THRUST 0x8000
#define RO_IO_P1FIRE 0x2000

#define RO_IO_P2START 0x08  // 2-player start
#define RO_IO_P2LEFT 0x01
#define RO_IO_P2RIGHT 0x04
#define RO_IO_P2THRUST 0x10
#define RO_IO_P2FIRE 0x20

#define RO_SW_ABORT SW_ABORT /* for ioSwitches */
#define RO_SW_COIN 0x080

  // static int prevButtonState = 0;  // for debouncing

  frameCounter += 1;
  // DEBUG_OUT("// Frame %d\n", frameCounter);

  // v_WaitRecal();
  // v_doSound();
  // v_readButtons();  // update currentButtonState
  // v_readJoystick1Analog();
  //v_readJoystick2Analog ();  // Apparently we are getting joystick 2 data anyway?????
  // v_playAllSFX();

  // Unfortunately, it's quite common to press LEFT and RIGHT simultaneously by accident with this
  // layout, and accidentally invoke the configuration screen.  Need to think about how we will
  // handle this...

  // default inactive:
  ioInputs = initialInputs | RO_IO_P1LEFT | RO_IO_P1RIGHT | RO_IO_P1THRUST | RO_IO_P1FIRE | RO_IO_P1START | RO_IO_P2LEFT | RO_IO_P2RIGHT | RO_IO_P2THRUST | RO_IO_P2FIRE | RO_IO_P2START;
  ioSwitches = initialSwitches | RO_SW_COIN;

  // digital joysticks...
  // commented out to get it to compile
  /* if (currentJoy1X < -30) ioInputs &= ~RO_IO_P1LEFT;
   if (currentJoy1X > 30) ioInputs &= ~RO_IO_P1RIGHT;
   if (currentJoy1Y > 30) ioInputs &= ~RO_IO_P1THRUST;

   if (currentJoy2X < -30) ioInputs &= ~RO_IO_P2LEFT;
   if (currentJoy2X > 30) ioInputs &= ~RO_IO_P2RIGHT;
   if (currentJoy2Y > 30) ioInputs &= ~RO_IO_P2THRUST;

   // would be helpful to examine ram and make these context-dependent

   if ((currentButtonState & ~prevButtonState) & (VEC_BUTTON_1_1 | VEC_BUTTON_2_1)) ioSwitches &= ~RO_SW_COIN;	// only on rising edge */


  // if (currentButtonState & VEC_BUTTON_1_2) ioInputs &= ~RO_IO_P1START; // needs 1 coin
#ifdef VSTCM
  // Update the button objects
  button2.update();
  // middle button on PCB starts game
  if (button2.fell()) {
    ioSwitches &= ~RO_SW_COIN;
    ioInputs &= ~RO_IO_P1START;  // needs 1 coin
  }
#endif
  /* if (currentButtonState & VEC_BUTTON_2_2) ioInputs &= ~RO_IO_P2START; // needs 2 coins and second controller

   if (currentButtonState & VEC_BUTTON_1_1) ioInputs &= ~RO_IO_P1LEFT;
   if (currentButtonState & VEC_BUTTON_1_2) ioInputs &= ~RO_IO_P1RIGHT;
   if (currentButtonState & VEC_BUTTON_1_3) ioInputs &= ~RO_IO_P1THRUST;
   if (currentButtonState & VEC_BUTTON_1_4) ioInputs &= ~RO_IO_P1FIRE;

   if (currentButtonState & VEC_BUTTON_2_1) ioInputs &= ~RO_IO_P2LEFT;
   if (currentButtonState & VEC_BUTTON_2_2) ioInputs &= ~RO_IO_P2RIGHT;
   if (currentButtonState & VEC_BUTTON_2_3) ioInputs &= ~RO_IO_P2THRUST;
   if (currentButtonState & VEC_BUTTON_2_4) ioInputs &= ~RO_IO_P2FIRE;
   prevButtonState = currentButtonState;
*/
#ifdef NEVER
  /*
# Initialization file for Rip Off (Single Player)
>
>*** Rip Off (Single Player) ***
>
>Keyboard Mapping:
>
>   One Player  = F1
>   Two Players = F2
>   Coin        = F3
>   Reset Game  = F4
>   Exit        = <Esc>
>
>   Left        = 'Z'
>   Right       = 'X'
>   Thrust      = '.'
>   Fire        = '/'

 ; Switch definitions:
 ;
 ;   D------  0=Normal, 1=Diagnostics
 ;   -O-----  0=Individual Scores, 1=Combined Scores
 ;   --S----  0=Sound in attract mode, 1=No Sound (sound not supported)
 ;
 ;   ---CC--  11 = 1 credit per 1 quarter
 ;            10 = 1 credit per 2 quarters
 ;            01 = 3 credits per 2 quarters
 ;            00 = 3 credits per 4 quarters
 ;
 ;   -----TT  11 = 12 fuel pods
 ;            10 = 4 fuel pods
 ;            00 = 8 fuel pods
 ;            01 = 16 fuel pods

 Switches=0011101

[Inputs]
 RstCPU  = 02000000,FFFFFFFF,00000000,FFFFFFFF	; Set bit indicating RESET
 Exit    = 01000000,FFFFFFFF,00000000,FFFFFFFF	; Set bit indicating Exit 
 Coin    = 00000000,FFFFFFFF,00000000,FF7FFFFF

 Player1 = 00000000,FFFFFFFD,00000002,FFFFFFFF
 Player2 = 00000000,FFFFFFF7,00000008,FFFFFFFF

 RFire   = 00000000,FFFFDFFF,00002000,FFFFFFFF
 RThrust = 00000000,FFFF7FFF,00008000,FFFFFFFF
 RRight  = 00000000,FFFFBFFF,00004000,FFFFFFFF
 RLeft   = 00000000,FFFFEFFF,00001000,FFFFFFFF

 LFire   = 00000000,FFFFFFDF,00000020,FFFFFFFF
 LThrust = 00000000,FFFFFFEF,00000010,FFFFFFFF
 LRight  = 00000000,FFFFFFFB,00000004,FFFFFFFF
 LLeft   = 00000000,FFFFFFFE,00000001,FFFFFFFF
   */
#endif
}

#ifdef NEVER
void spacewar_input() {
  //Spacewar inputs
  ioInputs = 0xffff;

  ioSwitches = 0x00cf;  //00ff=45 00ef=2min  00df 1:30 00cf 1min
  // if (GkeyCheck(config.kcoin1)){ioSwitches &= ~SW_COIN;}

  if (key[config.kp1left]) { ioInputs -= 0x0100; }
  if (key[config.kp1right]) { ioInputs -= 0x2000; }
  if (key[config.kp1but1]) { ioSwitches -= 0x04; }
  if (key[config.kp1but2]) { ioInputs -= 0x8000; }
  if (key[config.kp1but3]) { ioSwitches -= 0x02; }

  if (key[config.kp2left]) { ioInputs -= 0x4000; }
  if (key[config.kp2right]) { ioInputs -= 0x1000; }
  if (key[config.kp2but1]) { ioSwitches -= 0x01; }
  if (key[config.kp2but2]) { ioInputs -= 0x0200; }
  if (key[config.kp2but3]) { ioSwitches -= 0x08; }

  if (key[config.pad9]) { ioInputs -= 0x0008; }
  if (key[config.pad8]) { ioInputs -= 0x0002; }
  if (key[config.pad7]) { ioInputs -= 0x0080; }
  if (key[config.pad6]) { ioInputs -= 0x0020; }
  if (key[config.pad5]) { ioInputs -= 0x0400; }
  if (key[config.pad4]) { ioInputs -= 0x0004; }
  if (key[config.pad3]) { ioInputs -= 0x0001; }
  if (key[config.pad2]) { ioInputs -= 0x0040; }
  if (key[config.pad1]) { ioInputs -= 0x0010; }
  if (key[config.pad0]) { ioInputs -= 0x0800; }
}
#endif

void startFrame_spacewars(void) {

#define SW_IO_P1LEFT 0x0100
#define SW_IO_P1RIGHT 0x2000
#define SW_IO_P1THRUST 0x8000

#define SW_SW_P1FIRE 0x04
#define SW_SW_P1HYPER 0x02  // not yet assigned to a key

#define SW_IO_P2LEFT 0x4000
#define SW_IO_P2RIGHT 0x1000
#define SW_IO_P2THRUST 0x0200

#define SW_SW_P2FIRE 0x01
#define SW_SW_P2HYPER 0x08  // not yet assigned to a key

// not yet assigned to keys:
#define SW_IO_Zero 0x0800
#define SW_IO_One 0x0010
#define SW_IO_Two 0x0040
#define SW_IO_Three 0x0001
#define SW_IO_Four 0x0004
#define SW_IO_Five 0x0400
#define SW_IO_Six 0x0020
#define SW_IO_Seven 0x0080
#define SW_IO_Eight 0x0002
#define SW_IO_Nine 0x0008

#define SW_SW_ABORT SW_ABORT /* for ioSwitches */
#define SW_SW_COIN 0x080

  // Default of Switches=0000011 doesn't seem compatible with SW_SW_P2FIRE=0x01 and SW_SW_P1HYPER=0x02
  // Code from AAE above suggests the duration bits are the high two bits rather than the low two,
  // so either we have a big/little-endian situation, or it's something to do with the shuffling of
  // switch bits also mentioned in the AAE code. (not shown)

  // static int prevButtonState = 0;  // for debouncing

  frameCounter += 1;
  // DEBUG_OUT("// %d\n", frameCounter);

  //  v_WaitRecal();
  // v_doSound();
  // v_readButtons();  // update currentButtonState
  //  v_readJoystick1Analog();
  //v_readJoystick2Analog ();  // NOT YET IMPLEMENTED.
  // v_playAllSFX();

  // Unfortunately, it's quite common to press LEFT and RIGHT simultaneously by accident with this
  // layout, and accidentally invoke the configuration screen.  Need to think about how we will
  // handle this...

  // default inactive:
  ioInputs = initialInputs | 0xffff;
  ioSwitches = initialSwitches | 0x00cf;  // force for now...

  ioInputs |= SW_IO_P1LEFT | SW_IO_P1RIGHT | SW_IO_P1THRUST
              | SW_IO_P2LEFT | SW_IO_P2RIGHT | SW_IO_P2THRUST
              | SW_IO_Zero | SW_IO_One | SW_IO_Two | SW_IO_Three | SW_IO_Four | SW_IO_Five | SW_IO_Six | SW_IO_Seven | SW_IO_Eight | SW_IO_Nine;

  ioSwitches |= SW_SW_COIN | SW_SW_P1FIRE | SW_SW_P1HYPER | SW_SW_P2FIRE | SW_SW_P2HYPER;
/*   if ((currentButtonState & ~prevButtonState) & (VEC_BUTTON_1_1|VEC_BUTTON_1_1)) ioSwitches &= ~SW_SW_COIN;	// only on rising edge
   prevButtonState = currentButtonState;

   // digital joysticks
   if (currentJoy1X < -30) ioInputs &= ~SW_IO_P1LEFT;
   if (currentJoy1X > 30) ioInputs &= ~SW_IO_P1RIGHT;
   if (currentJoy1Y < -30) ioSwitches &= ~SW_SW_P1HYPER;
   if (currentJoy1Y > 30) ioInputs &= ~SW_IO_P1THRUST;

   if (currentJoy2X < -30) ioInputs &= ~SW_IO_P2LEFT;
   if (currentJoy2X > 30) ioInputs &= ~SW_IO_P2RIGHT;
   if (currentJoy2Y < -30) ioSwitches &= ~SW_SW_P2HYPER;
   if (currentJoy2Y > 30) ioInputs &= ~SW_IO_P2THRUST;

   if (currentButtonState & VEC_BUTTON_1_1) ioInputs &= ~SW_IO_P1LEFT;
   if (currentButtonState & VEC_BUTTON_1_2) ioInputs &= ~SW_IO_P1RIGHT;
   if (currentButtonState & VEC_BUTTON_1_3) ioInputs &= ~SW_IO_P1THRUST;
   if (currentButtonState & VEC_BUTTON_1_4) ioSwitches &= ~SW_SW_P1FIRE;

   if (currentButtonState & VEC_BUTTON_2_1) ioInputs &= ~SW_IO_P2LEFT;
   if (currentButtonState & VEC_BUTTON_2_2) ioInputs &= ~SW_IO_P2RIGHT;
   if (currentButtonState & VEC_BUTTON_2_3) ioInputs &= ~SW_IO_P2THRUST;
   if (currentButtonState & VEC_BUTTON_2_4) ioSwitches &= ~SW_SW_P2FIRE;
*/
#ifdef NEVER
  /*
# Initialization file for Space Wars
>
>*** Space Wars ***
>
>Keyboard Mapping:
>
>   Coin       = F3
>   Reset Game = F4
>   Exit       = <Esc>
>
>   Left Player       Right Player
>   ------------      ----------------------------------
>   Left   = 'Q'       Left   = Keypad '7'
>   Right  = 'A'       Right  = Keypad '5'
>   Walk   = 'X'       Walk   = Keypad '9'
>   Fire   = 'C'       Fire   = Keypad '-' or <Sysreq>
>   HyperS = <Alt>     HyperS = Keypad '+' or <Enter>
>   HyperS = <Ctrl>
>
>   Option keys     = '0'-'9'
>   Space War RESET = <Backspace>

 ; Switch definitions:
 ;
 ;   XXXXX--  Unused (Must be 0)
 ;
 ;   -----TT  00 = 0:45 minutes per coin
 ;            11 = 1:00 minutes per coin
 ;            10 = 1:30 minutes per coin
 ;            01 = 2:00 minutes per coin

 Switches=0000011

[Inputs]
 RstCPU   = 02000000,FFFFFFFF,00000000,FFFFFFFF	; Set bit indicating reset
 Exit     = 01000000,FFFFFFFF,00000000,FFFFFFFF ; Set bit indicating Exit 
 Coin     = 00000000,FFFFFFFF,00000000,FF7FFFFF

 ; Options

 Zero    = 00000000,FFFFF7FF,00000800,FFFFFFFF
 One     = 00000000,FFFFFFEF,00000010,FFFFFFFF
 Two     = 00000000,FFFFFFBF,00000040,FFFFFFFF
 Three   = 00000000,FFFFFFFE,00000001,FFFFFFFF
 Four    = 00000000,FFFFFFFB,00000004,FFFFFFFF
 Five    = 00000000,FFFFFBFF,00000400,FFFFFFFF
 Six     = 00000000,FFFFFFDF,00000020,FFFFFFFF
 Seven   = 00000000,FFFFFF7F,00000080,FFFFFFFF
 Eight   = 00000000,FFFFFFFD,00000002,FFFFFFFF
 Nine    = 00000000,FFFFFFF7,00000008,FFFFFFFF

 Reset   = 00000000,FFBFFFFF,00400000,FFFFFFFF

 ; Left player

 LLeft   = 00000000,FFFFFEFF,00000100,FFFFFFFF
 LRight  = 00000000,FFFFDFFF,00002000,FFFFFFFF
 LThrust = 00000000,FFFF7FFF,00008000,FFFFFFFF
 LFire   = 00000000,FFFBFFFF,00040000,FFFFFFFF
 LHyper  = 00000000,FFFDFFFF,00020000,FFFFFFFF

 ; Right player

 RLeft   = 00000000,FFFFBFFF,00004000,FFFFFFFF
 RRight  = 00000000,FFFFEFFF,00001000,FFFFFFFF
 RThrust = 00000000,FFFFFDFF,00000200,FFFFFFFF
 RFire   = 00000000,FFFEFFFF,00010000,FFFFFFFF
 RHyper  = 00000000,FFF7FFFF,00080000,FFFFFFFF
   */
#endif
}

void startFrame_boxingbugs(void) {
#define BB_SW_ABORT SW_ABORT /* for ioSwitches */
#define BB_SW_COIN 0x80

#define BB_IO_P1Panic 0x08   // Right Panic / One Player
#define BB_IO_P1Glove 0x10   // Right Glove
#define BB_IO_P1Cannon 0x20  // Right Cannon
#define BB_IO_P2Cannon 0x01  // Left Cannon
#define BB_IO_P2Glove 0x02   // Left Glove
#define BB_IO_P2Panic 0x04   // Left Panic / Two Player

#define BB_IO_Acct 0x40  // Accounting info on/off - is this a switch?

  // static int prevButtonState = 0;  // for debouncing
  frameCounter += 1;
  //  DEBUG_OUT("v_WaitRecal(); v_setBrightness(64);v_readButtons();v_readJoystick1Analog(); // %d\n", frameCounter);

  //  v_WaitRecal();
  // v_doSound();
  //  v_readButtons();  // update currentButtonState
  // v_readJoystick1Analog();
  // v_playAllSFX();

  ioSwitches = initialSwitches | BB_SW_COIN;
  ioInputs = initialInputs | BB_IO_P1Cannon | BB_IO_P1Glove | BB_IO_P1Panic | BB_IO_P2Cannon | BB_IO_P2Glove | BB_IO_P2Panic | BB_IO_Acct;

/*   if ((currentButtonState & ~prevButtonState) & (VEC_BUTTON_1_1 | VEC_BUTTON_2_1)) ioSwitches &= ~BB_SW_COIN;	// only on rising edge
   prevButtonState = currentButtonState;


   // this game needs special handling for the joystick... TO DO.

   // testing both to see which one it is...
   if (currentButtonState & VEC_BUTTON_1_1) ioInputs &= ~BB_IO_Acct;   // right does inputs
   
   if (currentButtonState & VEC_BUTTON_1_2) ioInputs &= ~BB_IO_P1Cannon;
   if (currentButtonState & VEC_BUTTON_1_3) ioInputs &= ~BB_IO_P1Glove;
   if (currentButtonState & VEC_BUTTON_1_4) ioInputs &= ~BB_IO_P1Panic;

   if (currentButtonState & VEC_BUTTON_2_2) ioInputs &= ~BB_IO_P2Cannon;
   if (currentButtonState & VEC_BUTTON_2_3) ioInputs &= ~BB_IO_P2Glove;
   if (currentButtonState & VEC_BUTTON_2_4) ioInputs &= ~BB_IO_P2Panic;
*/
#ifdef NEVER
  /*
# Initialization file for Boxing Bugs
>
>*** Boxing Bugs ***
>
>Keyboard Mapping:
>
>   One Player  = F1
>   Two Players = F2
>   Coin        = F3
>   Reset Game  = F4
>   Exit        = <Esc>
>
>   Cannon      = First (Left) Mouse Button
>   Glove       = Second Mouse Button
>   Panic       = Third Mouse Button
>   Panic       = <Spacebar>  (For the "third button challenged" mice)
>
>   Use mouse to aim Cannon/Glove.

; Switch definitions:
 ;
 ;   D------  0=Normal, 1=Diagnositic Mode
 ;   -F-----  0=Normal, 1=Free Play
 ;   --S----  0=No sound during attract, 1=Sound during attract (sound not supported)
 ;   ---B---  0=Bonus at 50k, 1=Bonus at 30k
 ;   ----P--  0=3 cannons per game, 1=5 cannons per game
 ;
 ;   -----CC  00 = 1 credit per 1 quarter
 ;            10 = 1 credit per 2 quarters
 ;            01 = 3 credits per 2 quarters
 ;            11 = 3 credits per 4 quarters

 Switches=0001100

[Inputs]
 RstCPU  = 02000000,FFFFFFFF,00000000,FFFFFFFF	; Set bit indicating RESET
 Exit    = 01000000,FFFFFFFF,00000000,FFFFFFFF	; Set bit indicating Exit 
 Coin    = 00000000,FFFFFFFF,00000000,FF7FFFFF

 ; Define Boxing Bug control panel

 LCannon = 00000000,FFFFFFFE,00000001,FFFFFFFF ; Left Cannon
 LGlove  = 00000000,FFFFFFFD,00000002,FFFFFFFF ; Left Glove
 LPanic  = 00000000,FFFFFFFB,00000004,FFFFFFFF ; Left Panic / Two Player
 RPanic  = 00000000,FFFFFFF7,00000008,FFFFFFFF ; Right Panic / One Player
 RGlove  = 00000000,FFFFFFEF,00000010,FFFFFFFF ; Right Glove
 RCannon = 00000000,FFFFFFDF,00000020,FFFFFFFF ; Right Cannon
 AcctOn  = 00000000,FFFFFFBF,00000000,FFFFFFFF ; Accounting Info On
 AcctOff = 00000040,FFFFFFFF,00000000,FFFFFFFF ; Accounting Info Off
   */
#endif
}

void startFrame_armorattack(void) {

#define AA_IO_P1START 0x02  // 1-player start
#define AA_IO_P1LEFT 0x1000
#define AA_IO_P1RIGHT 0x4000
#define AA_IO_P1THRUST 0x8000
#define AA_IO_P1FIRE 0x2000

#define AA_IO_P2START 0x08  // 2-player start
#define AA_IO_P2LEFT 0x01
#define AA_IO_P2RIGHT 0x04
#define AA_IO_P2THRUST 0x10
#define AA_IO_P2FIRE 0x20

#define AA_SW_ABORT SW_ABORT /* for ioSwitches */
#define AA_SW_COIN 0x080

  // static int prevButtonState = 0;  // for debouncing
  static int isInit = 0;

  frameCounter += 1;
  // DEBUG_OUT("// Frame %d\n", frameCounter);

  // v_WaitRecal();
  // v_doSound();
  //  v_readButtons();  // update currentButtonState
  //  v_readJoystick1Analog();
  //v_readJoystick2Analog ();  // Apparently we are getting joystick 2 data anyway?????
  // v_playAllSFX();

  // Unfortunately, it's quite common to press LEFT and RIGHT simultaneously by accident with this
  // layout, and accidentally invoke the configuration screen.  Need to think about how we will
  // handle this...

  // default inactive:
  if (isInit == 0) {
    isInit = 1;
    ioInputs = initialInputs | AA_IO_P1LEFT | AA_IO_P1RIGHT | AA_IO_P1THRUST | AA_IO_P1FIRE | AA_IO_P1START | AA_IO_P2LEFT | AA_IO_P2RIGHT | AA_IO_P2THRUST | AA_IO_P2FIRE | AA_IO_P2START;
    ioSwitches = initialSwitches | AA_SW_COIN;
  } else {
    ioInputs = AA_IO_P1LEFT | AA_IO_P1RIGHT | AA_IO_P1THRUST | AA_IO_P1FIRE | AA_IO_P1START | AA_IO_P2LEFT | AA_IO_P2RIGHT | AA_IO_P2THRUST | AA_IO_P2FIRE | AA_IO_P2START;
    ioSwitches = AA_SW_COIN;
  }

  /* if ((currentButtonState & ~prevButtonState) & (VEC_BUTTON_1_1 | VEC_BUTTON_2_1)) ioSwitches &= ~AA_SW_COIN;	// only on rising edge
   prevButtonState = currentButtonState;

   // digital joysticks...
   if (currentJoy1X < -30) ioInputs &= ~AA_IO_P1LEFT;
   if (currentJoy1X > 30) ioInputs &= ~AA_IO_P1RIGHT;
   if (currentJoy1Y > 30) ioInputs &= ~AA_IO_P1THRUST;

   if (currentJoy2X < -30) ioInputs &= ~AA_IO_P2LEFT;
   if (currentJoy2X > 30) ioInputs &= ~AA_IO_P2RIGHT;
   if (currentJoy2Y > 30) ioInputs &= ~AA_IO_P2THRUST;

   // would be helpful to examine ram and make these context-dependent

   if (currentButtonState & VEC_BUTTON_1_2) ioInputs &= ~AA_IO_P1START; // needs 1 coin
   if (currentButtonState & VEC_BUTTON_2_2) ioInputs &= ~AA_IO_P2START; // needs 2 coins and second controller

   if (currentButtonState & VEC_BUTTON_1_1) ioInputs &= ~AA_IO_P1LEFT;
   if (currentButtonState & VEC_BUTTON_1_2) ioInputs &= ~AA_IO_P1RIGHT;
   if (currentButtonState & VEC_BUTTON_1_3) ioInputs &= ~AA_IO_P1THRUST;
   if (currentButtonState & VEC_BUTTON_1_4) ioInputs &= ~AA_IO_P1FIRE;

   if (currentButtonState & VEC_BUTTON_2_1) ioInputs &= ~AA_IO_P2LEFT;
   if (currentButtonState & VEC_BUTTON_2_2) ioInputs &= ~AA_IO_P2RIGHT;
   if (currentButtonState & VEC_BUTTON_2_3) ioInputs &= ~AA_IO_P2THRUST;
   if (currentButtonState & VEC_BUTTON_2_4) ioInputs &= ~AA_IO_P2FIRE;
*/
#ifdef NEVER
  /*
>
>*** Armor Attack ***
>
>Keyboard Mapping:
>
>   Coin        = B1
>   One Player  = B2
>   Two Players = B3
>
>   Exit        = F1,F2,F3,F4
>   Calibrate   = F1,F2
>
>   Left        = F1
>   Right       = F2
>   Thrust      = F3
>   Fire        = F4
>

      
 ; Switch definitions:
 ;
 ;   D------  0=Diagnostics, 1=Normal
 ;   -X-----  Unused
 ;   --S----  0=No Sound in attract mode, 1=Sound (sound not supported)
 ;
 ;   ---CC--  00 = 1 credit per 1 quarter
 ;            10 = 1 credit per 2 quarters
 ;            01 = 3 credits per 2 quarters
 ;            11 = 3 credits per 4 quarters
 ;
 ;   -----JJ  00 = 5 jeeps per game
 ;   -----JJ  10 = 4 jeeps per game
 ;   -----JJ  01 = 3 jeeps per game
 ;   -----JJ  11 = 2 jeeps per game

 Switches=1000000      ; diagnostics, no sound, 1 credit per quarter, 5 jeeps per game ???

[Inputs]
 RstCPU  = 02000000,FFFFFFFF,00000000,FFFFFFFF	; Set bit indicating RESET
 Exit    = 01000000,FFFFFFFF,00000000,FFFFFFFF	; Set bit indicating Exit
 Coin    = 00000000,FFFFFFFF,00000000,FF7FFFFF

 Player1 = 00000000,FFFFFFFD,00000002,FFFFFFFF
 Player2 = 00000000,FFFFFFF7,00000008,FFFFFFFF

 RFire   = 00000000,FFFFDFFF,00002000,FFFFFFFF
 RThrust = 00000000,FFFF7FFF,00008000,FFFFFFFF
 RRight  = 00000000,FFFFBFFF,00004000,FFFFFFFF
 RLeft   = 00000000,FFFFEFFF,00001000,FFFFFFFF

 LFire   = 00000000,FFFFFFDF,00000020,FFFFFFFF
 LThrust = 00000000,FFFFFFEF,00000010,FFFFFFFF
 LRight  = 00000000,FFFFFFFB,00000004,FFFFFFFF
 LLeft   = 00000000,FFFFFFFE,00000001,FFFFFFFF
   */
#endif
}

void startFrame_starcastle(void) {
  //static int prevButtonState;	// for debouncing

  frameCounter += 1;
  // DEBUG_OUT("v_WaitRecal(); v_setBrightness(64);v_readButtons();v_readJoystick1Analog(); // %d\n", frameCounter);

//  v_WaitRecal();
// v_doSound();
//prevButtonState = currentButtonState;
//  v_readButtons();  // update currentButtonState
//  v_readJoystick1Analog();
// v_playAllSFX();
#ifdef NEVER
  /*
# Initialization file for Star Castle
>
>*** Star Castle ***
>
>Keyboard Mapping:
>
>   One Player  = F1
>   Two Players = F2
>   Coin        = F3
>   Reset Game  = F4
>   Exit        = <Esc>
>
>   Left        = 'Z'
>   Right       = 'X'
>   Thrust      = '.'
>   Fire        = '/'

 ; Switch definitions:
 ;
 ;   D------  0=Test Pattern, 1=Normal
 ;   -XX----  Unused
 ;
 ;   ---CC--  00 = 1 credit per 1 quarter
 ;            10 = 1 credit per 2 quarters
 ;            01 = 3 credit per 2 quarters
 ;            11 = 3 credit per 4 quarters
 ;
 ;   -----SS  00 = 3 ships per game
 ;            10 = 4 ships per game
 ;            01 = 5 ships per game
 ;            11 = 6 ships per game

 Switches=1000011

[Inputs]
 RstCPU  = 02000000,FFFFFFFF,00000000,FFFFFFFF	; Set bit indicating RESET
 Exit    = 01000000,FFFFFFFF,00000000,FFFFFFFF	; Set bit indicating Exit 
 Coin    = 00000000,FFFFFFFF,00000000,FF7FFFFF

 Player1 = 00000000,FFFFFFFE,00000001,FFFFFFFF
 Player2 = 00000000,FFFFFFFB,00000004,FFFFFFFF

 Left    = 00000000,FFFFFFBF,00000040,FFFFFFFF
 Right   = 00000000,FFFFFEFF,00000100,FFFFFFFF
 Thrust  = 00000000,FFFFFBFF,00000400,FFFFFFFF
 Fire    = 00000000,FFFFEFFF,00001000,FFFFFFFF
   */
#endif
}

void startFrame_starhawk(void) {
  // static int prevButtonState = 0;  // for debouncing

  frameCounter += 1;
  // DEBUG_OUT("// Frame %d\n", frameCounter);

  //  v_WaitRecal();
  // v_doSound();
  // v_readButtons();  // update currentButtonState
  // v_readJoystick1Analog();
  //v_readJoystick2Analog ();  // Apparently we are getting joystick 2 data anyway?????
  // v_playAllSFX();

#define SH_SW_P1_START 0x01
#define SH_IO_P1_LEFT 0x0002
#define SH_IO_P1_RIGHT 0x0004
#define SH_IO_P1_UP 0x0001
#define SH_IO_P1_DOWN 0x0008
#define SH_SW_P1_FIRE 0x08
#define SH_IO_P1_SLOW 0x4000
#define SH_IO_P1_MED 0x1000
#define SH_IO_P1_FAST 0x0200

#define SH_SW_P2_START 0x04
#define SH_IO_P2_LEFT 0x0400
#define SH_IO_P2_RIGHT 0x0010
#define SH_IO_P2_UP 0x0800
#define SH_IO_P2_DOWN 0x0020
#define SH_SW_P2_FIRE 0x02
#define SH_IO_P2_SLOW 0x0100
#define SH_IO_P2_MED 0x2000
#define SH_IO_P2_FAST 0x8000

#define SH_SW_COIN 0x80

  ioSwitches = initialSwitches | SH_SW_COIN | SH_SW_P1_START | SH_SW_P2_START | SH_SW_P1_FIRE | SH_SW_P2_FIRE;
#ifdef VSTCM
  // Update the button objects
  button2.update();
  // middle button on PCB starts game
  if (button2.fell()) {
    ioSwitches &= ~SH_SW_COIN;
    ioInputs &= ~SH_SW_P1_START;  // needs 1 coin
  }
#endif
  /* if ((currentButtonState & ~prevButtonState) & (VEC_BUTTON_1_1|VEC_BUTTON_2_1)) ioSwitches &= ~SH_SW_COIN;	// only on rising edge

   ioInputs = initialInputs | SH_IO_P1_LEFT | SH_IO_P1_RIGHT | SH_IO_P1_UP | SH_IO_P1_DOWN | SH_IO_P1_SLOW | SH_IO_P1_MED | SH_IO_P1_FAST |
                              SH_IO_P2_LEFT | SH_IO_P2_RIGHT | SH_IO_P2_UP | SH_IO_P2_DOWN | SH_IO_P2_SLOW | SH_IO_P2_MED | SH_IO_P2_FAST;

   if (currentButtonState & VEC_BUTTON_1_2) ioSwitches &= ~SH_SW_P1_START;
   if (currentButtonState & VEC_BUTTON_2_2) ioSwitches &= ~SH_SW_P2_START;

   // Digital joysticks.  Need to do the same sort of hack as
   // in Tailgunner to allow analog injection of cursor values
   // btw the P2 joystick for some reason seems much more responsive!
   
   if (currentJoy1X < -30) ioInputs &= ~SH_IO_P1_LEFT;
   if (currentJoy1X > 30) ioInputs &= ~SH_IO_P1_RIGHT;
   if (currentJoy1Y > 30) ioInputs &= ~SH_IO_P1_UP;
   if (currentJoy1Y < -30) ioInputs &= ~SH_IO_P1_DOWN;

   if (currentJoy2X < -30) ioInputs &= ~SH_IO_P2_LEFT;
   if (currentJoy2X > 30) ioInputs &= ~SH_IO_P2_RIGHT;
   if (currentJoy2Y > 30) ioInputs &= ~SH_IO_P2_UP;
   if (currentJoy2Y < -30) ioInputs &= ~SH_IO_P2_DOWN;

   // again, some context-sensitive decoding will be needed
   
   if (currentButtonState & VEC_BUTTON_1_1) ioInputs &= ~SH_IO_P1_SLOW;
   if (currentButtonState & VEC_BUTTON_2_1) ioInputs &= ~SH_IO_P2_SLOW;

   if (currentButtonState & VEC_BUTTON_1_2) ioInputs &= ~SH_IO_P1_MED;
   if (currentButtonState & VEC_BUTTON_2_2) ioInputs &= ~SH_IO_P2_MED;

   if (currentButtonState & VEC_BUTTON_1_3) ioInputs &= ~SH_IO_P1_FAST;
   if (currentButtonState & VEC_BUTTON_2_3) ioInputs &= ~SH_IO_P2_FAST;

   if (currentButtonState & VEC_BUTTON_1_4) ioSwitches &= ~SH_SW_P1_FIRE;
   if (currentButtonState & VEC_BUTTON_2_4) ioSwitches &= ~SH_SW_P2_FIRE;
  prevButtonState = currentButtonState;
*/
#ifdef NEVER
  /*
# Initialization file for Star Hawk
>
>*** Star Hawk ***
>
>Keyboard Mapping:
>
>   One Player  = F1
>   Two Players = F2
>   Coin        = F3
>   Reset Game  = F4
>   Exit        = <Esc>
>
>   Left Player            Right Player
>   ------------           ----------------------
>   Slow  = '1'            Slow  = '0'
>   Med   = '2'            Med   = '-'
>   Fast  = '3'            Fast  = '='
>   Left  = 'F'            Left  = Keypad '4'
>   Right = 'H'            Right = Keypad '6'
>   Up    = 'T'            Up    = Keypad '8'
>   Down  = 'G' or 'V'     Down  = Keypad '5' or Keypad '2'
>   Fire  = <Left Shift>   Fire  = <Right Shift>

 Switches=0000000

[Inputs]
 RstCPU  = 02000000,FFFFFFFF,00000000,FFFFFFFF	; Set bit indicating RESET
 Exit    = 01000000,FFFFFFFF,00000000,FFFFFFFF	; Set bit indicating Exit 
 Coin    = 00000000,FFFFFFFF,00000000,FF7FFFFF

 Player1 = 00000000,FFFEFFFF,00010000,FFFFFFFF
 Player2 = 00000000,FFFBFFFF,00040000,FFFFFFFF

 RSlow   = 00000000,FFFFBFFF,00004000,FFFFFFFF
 RMed    = 00000000,FFFFEFFF,00001000,FFFFFFFF
 RFast   = 00000000,FFFFFDFF,00000200,FFFFFFFF
 RLeft   = 00000000,FFFFFFFD,00000002,FFFFFFFF
 RRight  = 00000000,FFFFFFFB,00000004,FFFFFFFF
 RUp     = 00000000,FFFFFFFE,00000001,FFFFFFFF
 RDown   = 00000000,FFFFFFF7,00000008,FFFFFFFF
 RFire   = 00000000,FFF7FFFF,00080000,FFFFFFFF

 LSlow   = 00000000,FFFFFEFF,00000100,FFFFFFFF
 LMed    = 00000000,FFFFDFFF,00002000,FFFFFFFF
 LFast   = 00000000,FFFF7FFF,00008000,FFFFFFFF
 LLeft   = 00000000,FFFFFBFF,00000400,FFFFFFFF
 LRight  = 00000000,FFFFFFEF,00000010,FFFFFFFF
 LUp     = 00000000,FFFFF7FF,00000800,FFFFFFFF
 LDown   = 00000000,FFFFFFDF,00000020,FFFFFFFF
 LFire   = 00000000,FFFDFFFF,00020000,FFFFFFFF
   */
#endif
}

void startFrame_solarquest(void) {
  //  static int prevButtonState = 0;  // for debouncing

  frameCounter += 1;
  // DEBUG_OUT("v_WaitRecal(); v_setBrightness(64);v_readButtons();v_readJoystick1Analog(); // %d\n", frameCounter);

  //  v_WaitRecal();
  // v_doSound();
  // v_readButtons();  // update currentButtonState
  //  v_readJoystick1Analog();
  // v_playAllSFX();

#define SQ_SW_COIN 0x80

  ioSwitches = initialSwitches | SQ_SW_COIN;
  /*  if ((currentButtonState & ~prevButtonState) & (VEC_BUTTON_1_1|VEC_BUTTON_2_1)) ioSwitches &= ~SQ_SW_COIN;	// only on rising edge
   ioInputs = initialInputs;
   prevButtonState = currentButtonState;
*/
#ifdef NEVER
  /*
# Initialization file for Solar Quest
>
>*** Solar Quest ***
>
>Keyboard Mapping:
>
>   One Player  = F1
>   Two Players = F2
>   Coin        = F3
>   Reset Game  = F4
>   Exit        = <Esc>
>
>   Left        = 'Z'
>   Right       = 'X'
>   HyperSpace  = 'C'
>
>   Nova        = ','
>   Thrust      = '.'
>   Fire        = '/'

 ; Switch definitions:
 ;
 ;    D------  0=Diagnostics, 1=Normal
 ;    -F-----  0=Normal, 1=Free play
 ;
 ;    --SS---  00 = 2 ships
 ;             10 = 3 ships
 ;             01 = 4 ships
 ;             11 = 5 ships
 ;
 ;    ----C-C  0-0 = 1 coin 1 credit
 ;             1-0 = 2 coin 1 credit
 ;             0-1 = 2 coin 3 credit
 ;             1-1 = 4 coin 3 credit
 ;
 ;    -----E-  0=25 captures for extra ship, 1=40 captures

 Switches=1011000

 ; Default inputs (used to set difficulty level):
 ;
 ;    FFFF = Level 1 (Easiest)
 ;    EFFF = Level 2
 ;    DFFF = Level 3
 ;    CFFF = Level 4
 ;    BFFF = Level 5
 ;    AFFF = Level 6
 ;    9FFF = Level 7
 ;    8FFF = Level 8 (Hardest)
 ;
 ; Any other settings may cause erratic behaviour!

 Inputs=FFFF

[Inputs]
 RstCPU  = 02000000,FFFFFFFF,00000000,FFFFFFFF	; Set bit indicating RESET
 Exit    = 01000000,FFFFFFFF,00000000,FFFFFFFF	; Set bit indicating Exit 
 Coin    = 00000000,FFFFFFFF,00000000,FF7FFFFF

 Player1 = 00000000,FFFFFFF7,00000008,FFFFFFFF	; Also Hyperspace key
 Player2 = 00000000,FFFFFFFE,00000001,FFFFFFFF	; Also Nova key
 Left    = 00000000,FFFFFFDF,00000020,FFFFFFFF
 Right   = 00000000,FFFFFFEF,00000010,FFFFFFFF
 Thrust  = 00000000,FFFFFFFB,00000004,FFFFFFFF
 Fire    = 00000000,FFFFFFFD,00000002,FFFFFFFF
   */
#endif
}

void startFrame_cosmicchasm(void) {
  //  static int prevButtonState = 0;  // for debouncing

  frameCounter += 1;
  //  DEBUG_OUT("v_WaitRecal(); v_setBrightness(64);v_readButtons();v_readJoystick1Analog(); // %d\n", frameCounter);

  //  v_WaitRecal();
  // v_doSound();
  // v_readButtons();  // update currentButtonState
  //  v_readJoystick1Analog();
  // v_playAllSFX();

#define CC_SW_COIN 0x80

  ioSwitches = initialSwitches | CC_SW_COIN;
  /*  if ((currentButtonState & ~prevButtonState) & (VEC_BUTTON_1_1|VEC_BUTTON_2_1)) ioSwitches &= ~CC_SW_COIN;	// only on rising edge
   prevButtonState = currentButtonState;
   ioInputs = initialInputs;
*/
#ifdef NEVER
  /*
# Initialization file for Cosmic Chasm - best guess, under development
>
>***Cosmic Chasm ***
>
>Keyboard Mapping:
>
>   One Player  = F1
>   Two Players = F2
>   Coin        = F3
>   Reset Game  = F4
>   Exit        = <Esc>
>

; Switch definitions:
 ;
 ;   D------  0=Normal, 1=Diagnositic Mode
 ;   -F-----  0=Normal, 1=Free Play
 ;   --S----  0=No sound during attract, 1=Sound during attract (sound not supported)
 ;   ---B---  0=Bonus at 50k, 1=Bonus at 30k
 ;   ----P--  0=3 cannons per game, 1=5 cannons per game
 ;
 ;   -----CC  00 = 1 credit per 1 quarter
 ;            10 = 1 credit per 2 quarters
 ;            01 = 3 credits per 2 quarters
 ;            11 = 3 credits per 4 quarters

 Switches=0001100

[Inputs]
 RstCPU  = 02000000,FFFFFFFF,00000000,FFFFFFFF	; Set bit indicating RESET
 Exit    = 01000000,FFFFFFFF,00000000,FFFFFFFF	; Set bit indicating Exit 
 Coin    = 00000000,FFFFFFFF,00000000,FF7FFFFF
   */
#endif
}

void startFrame_waroftheworlds(void) {
  //  static int prevButtonState = 0;  // for debouncing

  frameCounter += 1;
  // DEBUG_OUT("v_WaitRecal(); v_setBrightness(64);v_readButtons();v_readJoystick1Analog(); // %d\n", frameCounter);

  // v_WaitRecal();
  // v_doSound();
  // v_readButtons();  // update currentButtonState
  //  v_readJoystick1Analog();
  // v_playAllSFX();

#define WW_SW_COIN 0x80

  ioSwitches = initialSwitches | WW_SW_COIN;
  /*  if ((currentButtonState & ~prevButtonState) & (VEC_BUTTON_1_1|VEC_BUTTON_2_1)) ioSwitches &= ~WW_SW_COIN;	// only on rising edge
   prevButtonState = currentButtonState;
   ioInputs = initialInputs;
*/
#ifdef NEVER
  /*
# Initialization file for War of the Worlds
>
>*** War of the Worlds ***
>
>Keyboard Mapping:
>
>   One Player  = F1
>   Two Players = F2
>   Coin        = F3
>   Reset Game  = F4
>   Exit        = <Esc>
>
>   Left        = 'Z'
>   Right       = 'X'
>   Shields     = '.'
>   Fire        = '/'

 ; Switch definitions:
 ;
 ;   D------  0=Normal, 1=Diagnostics
 ;   -F-----  0=Normal, 1=Free Play
 ;   ---C---  0=1 credit per 1 quarter, 1=3 credits per 2 quarters
 ;   -----S-  0=5 ships per game, 1=3 ships per game
 ;
 ;   --?-?-?  *unknown* (no manual exists)

 Switches=0000000

[Inputs]
 RstCPU  = 02000000,FFFFFFFF,00000000,FFFFFFFF	; Set bit indicating RESET
 Exit    = 01000000,FFFFFFFF,00000000,FFFFFFFF	; Set bit indicating Exit 
 Coin    = 00000000,FFFFFFFF,00000000,FF7FFFFF

 Player1 = 00000000,FFFFFFFE,00000001,FFFFFFFF
 Player2 = 00000000,FFFFFFFB,00000004,FFFFFFFF

 Left    = 00000000,FFFFFFBF,00000040,FFFFFFFF
 Right   = 00000000,FFFFFEFF,00000100,FFFFFFFF
 Shields = 00000000,FFFFFBFF,00000400,FFFFFFFF
 Fire    = 00000000,FFFFEFFF,00001000,FFFFFFFF

   */
#endif
}

void startFrame_warrior(void) {
  // static int prevButtonState = 0;  // for debouncing

  frameCounter += 1;
  // DEBUG_OUT("// Frame %d\n", frameCounter);

  //  v_WaitRecal();
  // v_doSound();
  //  v_readButtons();  // update currentButtonState
  //  v_readJoystick1Analog();
  //v_readJoystick2Analog ();  // Apparently we are getting joystick 2 data anyway?????
  // v_playAllSFX();

  // Don't have any input for this game as to Player 1 or Player 2 start....

#define WA_SW_Sw0 0x01
#define WA_SW_Sw1 0x02
#define WA_SW_Sw2 0x04
#define WA_SW_Sw3 0x08
#define WA_SW_Sw6 0x40

  //#define WA_IO_P1_START 0x??
#define WA_IO_P1_LEFT 0x02
#define WA_IO_P1_RIGHT 0x01
#define WA_IO_P1_UP 0x04
#define WA_IO_P1_DOWN 0x08
#define WA_IO_P1_SWORD 0x10

  //#define WA_IO_P2_START 0x????
#define WA_IO_P2_LEFT 0x0200
#define WA_IO_P2_RIGHT 0x0100
#define WA_IO_P2_UP 0x0400
#define WA_IO_P2_DOWN 0x0800
#define WA_IO_P2_SWORD 0x1000

#define WA_SW_COIN 0x80

  ioSwitches = initialSwitches | WA_SW_COIN;
  //  if ((currentButtonState & ~prevButtonState) & (VEC_BUTTON_1_1|VEC_BUTTON_2_1)) ioSwitches &= ~WA_SW_COIN;	// only on rising edge

  //  prevButtonState = currentButtonState;
  ioInputs = initialInputs | /*WA_IO_P1_START |*/ WA_IO_P1_LEFT | WA_IO_P1_RIGHT | WA_IO_P1_UP | WA_IO_P1_DOWN | WA_IO_P1_SWORD |
             /*WA_IO_P2_START |*/ WA_IO_P2_LEFT | WA_IO_P2_RIGHT | WA_IO_P2_UP | WA_IO_P2_DOWN | WA_IO_P2_SWORD;

  // How to start?
  //if (currentButtonState & VEC_BUTTON_1_2) ioInputs &= ~WA_IO_P1_START;
  //if (currentButtonState & VEC_BUTTON_2_2) ioInputs &= ~WA_IO_P2_START;
#ifdef VSTCM
  // Update the button objects
  button2.update();
  // middle button on PCB starts game
  if (button2.fell()) {
    // ioSwitches &= ~TG_SW_COIN;
    //  ioInputs &= ~WA_IO_P2_START;
  }
#endif
  // USE JOYSTICK
  /*  if (currentJoy1X < -30) ioInputs &= ~WA_IO_P1_LEFT;
   if (currentJoy1X > 30) ioInputs &= ~WA_IO_P1_RIGHT;
   if (currentJoy1Y > 30) ioInputs &= ~WA_IO_P1_UP;
   if (currentJoy1Y < -30) ioInputs &= ~WA_IO_P1_DOWN;

   if (currentJoy2X < -30) ioInputs &= ~WA_IO_P2_LEFT;
   if (currentJoy2X > 30) ioInputs &= ~WA_IO_P2_RIGHT;
   if (currentJoy2Y > 30) ioInputs &= ~WA_IO_P2_UP;
   if (currentJoy2Y < -30) ioInputs &= ~WA_IO_P2_DOWN;

   if (currentButtonState & VEC_BUTTON_1_4) ioInputs &= ~WA_IO_P1_SWORD;
   if (currentButtonState & VEC_BUTTON_2_4) ioInputs &= ~WA_IO_P2_SWORD;
*/
#ifdef NEVER
  /*
# Initialization file for Warrior
>
>*** Warrior ***
>
>Keyboard Mapping:
>
>   One Player  = F1
>   Two Players = F2
>   Coin        = F3
>   Reset Game  = F4
>   Exit        = <Esc>
>
>   Left Player            Right Player
>   ------------           ----------------------
>   Left  = 'F'            Left  = Keypad '4'
>   Right = 'H'            Right = Keypad '6'
>   Up    = 'T'            Up    = Keypad '8'
>   Down  = 'G'            Down  = Keypad '5'
>   Sword = <Left Shift>   Sword = <Right Shift>

 Switches=1111111

[Inputs]
 RstCPU  = 02000000,FFFFFFFF,00000000,FFFFFFFF	; Set bit indicating RESET
 Exit    = 01000000,FFFFFFFF,00000000,FFFFFFFF	; Set bit indicating Exit
 Coin    = 00000000,FFFFFFFF,00000000,FF7FFFFF

 LRight  = 00000000,FFFFFEFF,00000100,FFFFFFFF
 LLeft   = 00000000,FFFFFDFF,00000200,FFFFFFFF
 LUp     = 00000000,FFFFFBFF,00000400,FFFFFFFF
 LDown   = 00000000,FFFFF7FF,00000800,FFFFFFFF
 LSword  = 00000000,FFFFEFFF,00001000,FFFFFFFF

 RRight  = 00000000,FFFFFFFE,00000001,FFFFFFFF
 RLeft   = 00000000,FFFFFFFD,00000002,FFFFFFFF
 RUp     = 00000000,FFFFFFFB,00000004,FFFFFFFF
 RDown   = 00000000,FFFFFFF7,00000008,FFFFFFFF
 RSword  = 00000000,FFFFFFEF,00000010,FFFFFFFF

 Sw0  = 00000000,FFFEFFFF,00010000,FFFFFFFF
 Sw1  = 00000000,FFFDFFFF,00020000,FFFFFFFF
 Sw2  = 00000000,FFFBFFFF,00040000,FFFFFFFF
 Sw3  = 00000000,FFF7FFFF,00080000,FFFFFFFF
 Sw6  = 00000000,FFBFFFFF,00400000,FFFFFFFF

 Key5 = 00000000,FFFFFFDF,00000020,FFFFFFFF
 Key6 = 00000000,FFFFFFBF,00000040,FFFFFFFF
 Key7 = 00000000,FFFFFF7F,00000080,FFFFFFFF
 KeyD = 00000000,FFFFDFFF,00002000,FFFFFFFF
 KeyE = 00000000,FFFFBFFF,00004000,FFFFFFFF
 KeyF = 00000000,FFFF7FFF,00008000,FFFFFFFF
   */
#endif
}

void startFrame_barrier(void) {
  //  static int prevButtonState = 0;  // for debouncing

  frameCounter += 1;
  // DEBUG_OUT("// Frame %d\n", frameCounter);

  // v_WaitRecal();
  // v_doSound();
  // v_readButtons();  // update currentButtonState
  // v_readJoystick1Analog();
  //v_readJoystick2Analog ();  // Apparently we are getting joystick 2 data anyway?????
  // v_playAllSFX();

#define BA_IO_P1_START 0x0800
#define BA_IO_P1_LEFT 0x4000
#define BA_IO_P1_RIGHT 0x0200
#define BA_IO_P1_FWD 0x1000
#define BA_IO_P1_REV 0x0008

#define BA_IO_P2_START 0x0010
#define BA_IO_P2_LEFT 0x0100
#define BA_IO_P2_RIGHT 0x8000
#define BA_IO_P2_FWD 0x2000
#define BA_IO_P2_REV 0x0400

#define BA_IO_SKILL_A 0X01
#define BA_IO_SKILL_B 0X04
#define BA_IO_SKILL_C 0X40

#define BA_SW_COIN 0x80

  ioSwitches = initialSwitches | BA_SW_COIN;
#ifdef VSTCM
  button2.update();
  // middle button on PCB starts game
  if (button2.fell()) {
    ioInputs &= ~BA_IO_P1_START;
  }
#endif
/*   if ((currentButtonState & ~prevButtonState) & (VEC_BUTTON_1_1|VEC_BUTTON_2_1)) ioSwitches &= ~BA_SW_COIN;	// only on rising edge

   ioInputs = initialInputs | BA_IO_P1_START | BA_IO_P1_LEFT | BA_IO_P1_RIGHT | BA_IO_P1_FWD | BA_IO_P1_REV |
                              BA_IO_P2_START | BA_IO_P2_LEFT | BA_IO_P2_RIGHT | BA_IO_P2_FWD | BA_IO_P2_REV |
                              BA_IO_SKILL_A | BA_IO_SKILL_B | BA_IO_SKILL_C;
// USE JOYSTICK
   if (currentJoy1X < -30) ioInputs &= ~BA_IO_P1_LEFT;
   if (currentJoy1X > 30) ioInputs &= ~BA_IO_P1_RIGHT;
   if (currentJoy1Y > 30) ioInputs &= ~BA_IO_P1_FWD;
   if (currentJoy1Y < -30) ioInputs &= ~BA_IO_P1_REV;

   if (currentJoy2X < -30) ioInputs &= ~BA_IO_P2_LEFT;
   if (currentJoy2X > 30) ioInputs &= ~BA_IO_P2_RIGHT;
   if (currentJoy2Y > 30) ioInputs &= ~BA_IO_P2_FWD;
   if (currentJoy2Y < -30) ioInputs &= ~BA_IO_P2_REV;

   if (currentButtonState & VEC_BUTTON_1_2) ioInputs &= ~BA_IO_P1_START;
   if (currentButtonState & VEC_BUTTON_2_2) ioInputs &= ~BA_IO_P2_START;

   if (currentButtonState & (VEC_BUTTON_1_3|VEC_BUTTON_2_3)) ioInputs &= ~BA_IO_SKILL_A; // MAYBE SKILL++ AND SKILL-- ? ONE BUTTON SHORT
   if (currentButtonState & (VEC_BUTTON_1_4|VEC_BUTTON_2_4)) ioInputs &= ~BA_IO_SKILL_C;
   prevButtonState = currentButtonState;
 */
#ifdef NEVER
  /*
# Initialization file for Barrier
>
>*** Barrier ***
>
>Keyboard Mapping:
>
>   One Player  = F1
>   Two Players = F2
>   Coin        = F3
>   Reset Game  = F4
>   Exit        = <Esc>
>
>   Left    = Keypad '4'     Skill A = '1'
>   Right   = Keypad '6'     Skill B = '2'
>   Forward = Keypad '8'     Skill C = '3'
>   Reverse = Keypad '2'
>
>   Use 'Forward', and any skill keys, to enter high score.

 ; Switch definitions:
 ;
 ;   XXXXX--  Unused
 ;   -----S-  0=Audio in attract mode, 1=No audio (sound not supported)
 ;   ------I  0=5 innings per game, 1=3 innings per game 

 Switches=0000001

[Inputs]
 RstCPU  = 02000000,FFFFFFFF,00000000,FFFFFFFF	; Set bit indicating RESET
 Exit    = 01000000,FFFFFFFF,00000000,FFFFFFFF	; Set bit indicating Exit 
 Coin    = 00000000,FFFFFFFF,00000000,FF7FFFFF

 Player1 = 00000000,FFFFF7FF,00000800,FFFFFFFF
 Player2 = 00000000,FFFFFFEF,00000010,FFFFFFFF

 SkillA  = 00000000,FFFFFFFE,00000001,FFFFFFFF
 SkillB  = 00000000,FFFFFFFB,00000004,FFFFFFFF
 SkillC  = 00000000,FFFFFFBF,00000040,FFFFFFFF

 ; Use these definitions if you want seperate player 1 & 2 controls
 ; (You'll have to define the player 2 keys you want to use in [KeyMapping])

; Left1    = 00000000,FFFFBFFF,00004000,FFFFFFFF
; Right1   = 00000000,FFFFFDFF,00000200,FFFFFFFF
; Fwd1     = 00000000,FFFFEFFF,00001000,FFFFFFFF
; Rev1     = 00000000,FFFFFFF7,00000008,FFFFFFFF

; Left2    = 00000000,FFFFFEFF,00000100,FFFFFFFF
; Right2   = 00000000,FFFF7FFF,00008000,FFFFFFFF
; Fwd2     = 00000000,FFFFDFFF,00002000,FFFFFFFF
; Rev2     = 00000000,FFFFFBFF,00000400,FFFFFFFF

 ; Use these definitions to have Player 1 and 2 share the same keys

 Left1&2  = 00000000,FFFFBEFF,00004100,FFFFFFFF
 Right1&2 = 00000000,FFFF7DFF,00008200,FFFFFFFF
 Fwd1&2   = 00000000,FFFFCFFF,00003000,FFFFFFFF
 Rev1&2   = 00000000,FFFFFBF7,00000408,FFFFFFFF

   */
#endif
}

void startFrame_sundance(void) {
  // need to check P1/P2 against L/R
#define SD_IO_P1START 0x04
#define SD_IO_P2START 0x08
#define SD_IO_GRID 0x20
#define SD_IO_2SUNS 0x0800
#define SD_IO_3SUNS 0x10
#define SD_IO_4SUNS 0x40
#define SD_IO_P1FIRE 0x02
#define SD_IO_P2FIRE 0x80

#define SD_SW_COIN 0x080
  //  static int prevButtonState = 0;  // for debouncing
  int Square, X, Y;

  frameCounter += 1;
  // DEBUG_OUT("// Frame %d\n", frameCounter);

  // v_WaitRecal();
  // v_doSound();
  //  v_readButtons();  // update currentButtonState
  // v_readJoystick1Analog();
  //v_readJoystick2Analog ();  // Apparently we are getting joystick 2 data anyway?????
  // v_playAllSFX();

  ioSwitches = initialSwitches | SD_SW_COIN;
  // if ((currentButtonState & ~prevButtonState) & VEC_BUTTON_1_1) ioSwitches &= ~SD_SW_COIN;	// only on rising edge

#define P1XLEFT 1
#define P1XCENT 2
#define P1XRIGHT 4
#define P1YTOP 8
#define P1YCENT 16
#define P1YBOT 32

  ioInputs = initialInputs | 0x5201 | 0xA580;
  X = P1XLEFT;
  Y = P1YBOT;
  // if (currentJoy1X > 30) X = P1XRIGHT; else if (currentJoy1X < -30) X = P1XLEFT; else X = P1XCENT;
  //  if (currentJoy1Y > 30) Y = P1YTOP; else if (currentJoy1Y < -30) Y = P1YBOT; else Y = P1YCENT;

  switch (X | Y) {
      /*
 Hatch1R = 00004000,FFFFEDFE,00005201,FFFFFFFF    1201
 Hatch2R = 00004201,FFFFEFFF,00005201,FFFFFFFF    1000
 Hatch3R = 00005200,FFFFFFFE,00005201,FFFFFFFF    0001
 Hatch4R = 00001201,FFFFBFFF,00005201,FFFFFFFF    4000
 Hatch5R = 00004200,FFFFEFFE,00005201,FFFFFFFF    1001
 Hatch6R = 00005001,FFFFFDFF,00005201,FFFFFFFF    0200
 Hatch7R = 00001200,FFFFBFFE,00005201,FFFFFFFF    4001
 Hatch8R = 00004001,FFFFEDFF,00005201,FFFFFFFF    1200
 Hatch9R = 00005000,FFFFFDFE,00005201,FFFFFFFF    0201
     */
    case P1XLEFT + P1YTOP: Square = 0x1201; break;
    case P1XCENT + P1YTOP: Square = 0x1000; break;
    case P1XRIGHT + P1YTOP: Square = 0x0001; break;

    case P1XLEFT + P1YCENT: Square = 0x4000; break;
    case P1XCENT + P1YCENT: Square = 0x1001; break;
    case P1XRIGHT + P1YCENT: Square = 0x0200; break;

    case P1XLEFT + P1YBOT: Square = 0x4001; break;
    case P1XCENT + P1YBOT: Square = 0x1200; break;
    case P1XRIGHT + P1YBOT: Square = 0x0201; break;
  }
  ioInputs &= ~Square;


#define P2XLEFT 1
#define P2XCENT 2
#define P2XRIGHT 4
#define P2YTOP 8
#define P2YCENT 16
#define P2YBOT 32


  // if (currentJoy2X > 30) X = P2XRIGHT; else if (currentJoy2X < -30) X = P2XLEFT; else X = P2XCENT;
  //  if (currentJoy2Y > 30) Y = P2YTOP; else if (currentJoy2Y < -30) Y = P2YBOT; else Y = P2YCENT;

  switch (X | Y) {
      /*
 Hatch1L = 00008080,FFFFDAFF,0000A580,FFFFFFFF   2500
 Hatch2L = 00008580,FFFFDFFF,0000A580,FFFFFFFF   2000
 Hatch3L = 0000A180,FFFFFBFF,0000A580,FFFFFFFF   0400

 Hatch4L = 00002580,FFFF7FFF,0000A580,FFFFFFFF   8000
 Hatch5L = 00008180,FFFFDBFF,0000A580,FFFFFFFF   2400
 Hatch6L = 0000A480,FFFFFEFF,0000A580,FFFFFFFF   0100

 Hatch7L = 00002180,FFFF7BFF,0000A580,FFFFFFFF   9400  <-- possibly should be A400 or 8400 ???
 Hatch8L = 00008480,FFFFDEFF,0000A580,FFFFFFFF   2100
 Hatch9L = 0000A080,FFFFFAFF,0000A580,FFFFFFFF   0500
     */
    case P2XLEFT + P2YTOP: Square = 0x2500; break;
    case P2XCENT + P2YTOP: Square = 0x2000; break;
    case P2XRIGHT + P2YTOP: Square = 0x0400; break;

    case P2XLEFT + P2YCENT: Square = 0x8000; break;
    case P2XCENT + P2YCENT: Square = 0x2400; break;
    case P2XRIGHT + P2YCENT: Square = 0x0100; break;

    case P2XLEFT + P2YBOT: Square = 0x9400; break;
    case P2XCENT + P2YBOT: Square = 0x2100; break;
    case P2XRIGHT + P2YBOT: Square = 0x0500; break;
  }
  ioInputs &= ~Square;
  ioInputs |= SD_IO_P1START | SD_IO_P2START | SD_IO_GRID | SD_IO_2SUNS | SD_IO_3SUNS | SD_IO_4SUNS | SD_IO_P1FIRE | SD_IO_P2FIRE;

  /*  if ((currentButtonState & ~prevButtonState) & (VEC_BUTTON_1_1|VEC_BUTTON_2_1)) ioSwitches &= ~SD_SW_COIN;	// only on rising edge
  if (currentButtonState & VEC_BUTTON_1_2) ioInputs &= ~SD_IO_P1START;
  if (currentButtonState & VEC_BUTTON_2_2) ioInputs &= ~SD_IO_P2START;
  if (currentButtonState & (VEC_BUTTON_1_3|VEC_BUTTON_2_3)) ioInputs &= ~SD_IO_GRID;
  if (currentButtonState & VEC_BUTTON_1_4) ioInputs &= ~SD_IO_P1FIRE;
  if (currentButtonState & VEC_BUTTON_2_4) ioInputs &= ~SD_IO_P2FIRE;
   prevButtonState = currentButtonState;
*/
#ifdef VSTCM
  button2.update();
  ioSwitches &= ~SD_SW_COIN;  // start adding credits
  // middle button on PCB starts game
  if (button2.fell()) {
    ioInputs &= ~SD_IO_P1START;
  }
#endif

#ifdef NEVER
  /*
# Initialization file for Sundance
>
>*** Sundance ***
>
>Keyboard Mapping:
>
>   One Player  = F1      Grid Control = '1'
>   Two Players = F2      2 Suns       = '2'
>   Coin        = F3      3 Suns       = '3'
>   Reset Game  = F4      4 Suns       = '4'
>   Exit        = <Esc>
>   
>   Left Player:          Right Player: 
>    -----------           -----------
>   | R | T | Y |         | 7 | 8 | 9 |
>   |---|---|---|         |---|---|---|
>   | F | G | H |         | 4 | 5 | 6 |
>   |---|---|---|         |---|---|---|
>   | V | B | N |         | 1 | 2 | 3 |
>    -----------           -----------
>   Fire = <Left Shift>   Fire = <Right Shift>

 ; Switch definitions:
 ;
 ;   XXX----  Unused
 ;   ---P---  0=2 players needs 2 coins, 1=2 players need only 1 coin
 ;   ----E--  0=Japanese, 1=English
 ;
 ;   -----TT  11 = 0:45 minutes per coin
 ;            01 = 1:00 minutes per coin
 ;            10 = 1:30 minutes per coin
 ;            00 = 2:00 minutes per coin

 Switches=0000101

[Inputs]
 RstCPU  = 02000000,FFFFFFFF,00000000,FFFFFFFF	; Set bit indicating RESET
 Exit    = 01000000,FFFFFFFF,00000000,FFFFFFFF	; Set bit indicating Exit 
 Coin    = 00000000,FFFFFFFF,00000000,FF7FFFFF

 Player1 = 00000000,FFFFFFFB,00000004,FFFFFFFF
 Player2 = 00000000,FFFFFFF7,00000008,FFFFFFFF

 Grid    = 00000000,FFFFFFDF,00000020,FFFFFFFF
 2Suns   = 00000000,FFFFF7FF,00000800,FFFFFFFF
 3Suns   = 00000000,FFFFFFEF,00000010,FFFFFFFF
 4Suns   = 00000000,FFFFFFBF,00000040,FFFFFFFF
 FireR   = 00000000,FFFFFFFD,00000002,FFFFFFFF
 FireL   = 00000000,FFFFFF7F,00000080,FFFFFFFF 

 Hatch1R = 00004000,FFFFEDFE,00005201,FFFFFFFF
 Hatch2R = 00004201,FFFFEFFF,00005201,FFFFFFFF
 Hatch3R = 00005200,FFFFFFFE,00005201,FFFFFFFF
 Hatch4R = 00001201,FFFFBFFF,00005201,FFFFFFFF
 Hatch5R = 00004200,FFFFEFFE,00005201,FFFFFFFF
 Hatch6R = 00005001,FFFFFDFF,00005201,FFFFFFFF
 Hatch7R = 00001200,FFFFBFFE,00005201,FFFFFFFF
 Hatch8R = 00004001,FFFFEDFF,00005201,FFFFFFFF
 Hatch9R = 00005000,FFFFFDFE,00005201,FFFFFFFF

 Hatch1L = 00008080,FFFFDAFF,0000A580,FFFFFFFF 
 Hatch2L = 00008580,FFFFDFFF,0000A580,FFFFFFFF 
 Hatch3L = 0000A180,FFFFFBFF,0000A580,FFFFFFFF 
 Hatch4L = 00002580,FFFF7FFF,0000A580,FFFFFFFF 
 Hatch5L = 00008180,FFFFDBFF,0000A580,FFFFFFFF 
 Hatch6L = 0000A480,FFFFFEFF,0000A580,FFFFFFFF 
 Hatch7L = 00002180,FFFF7BFF,0000A580,FFFFFFFF 
 Hatch8L = 00008480,FFFFDEFF,0000A580,FFFFFFFF 
 Hatch9L = 0000A080,FFFFFAFF,0000A580,FFFFFFFF 
   */
#endif
}

void startFrame_qb3(void) {
  // static int prevButtonState = 0;  // for debouncing

  frameCounter += 1;
  // DEBUG_OUT("v_WaitRecal(); v_setBrightness(64);v_readButtons();v_readJoystick1Analog(); // %d\n", frameCounter);

  //  v_WaitRecal();
  // v_doSound();
  // v_readButtons();  // update currentButtonState
  //  v_readJoystick1Analog();
  // v_playAllSFX();

#define QB_SW_COIN 0x80

  ioSwitches = initialSwitches | QB_SW_COIN;
  /*  if ((currentButtonState & ~prevButtonState) & (VEC_BUTTON_1_1|VEC_BUTTON_2_1)) ioSwitches &= ~QB_SW_COIN;	// only on rising edge
   prevButtonState = currentButtonState;
   ioInputs = initialInputs;
*/
#ifdef NEVER
  /*
# Initialization file for QB3 - under development
>
>*** QB3 ***
>
>Keyboard Mapping:
>
>   Start Game  = F1
>   Coin        = F3
>   Reset Game  = F4
>   Exit        = <Esc>
>


 Inputs=FFFF ; unknown for now # <input players="1" buttons="4" coins="1">
 Switches= 1001001000010   ; free play on
                      00   2 lives
                      01   4 lives
                      10   3 lives default
                      11   5 lives
                    1???   free play off  default
                    0???   free play on
                 1??????   service mode off  default
                 0??????   service mode on
              1?????????   debug off  default
              0?????????   debug on
           1????????????   infinite lives off  default
           0????????????   infinite lives on

[Inputs]
 RstCPU  = 02000000,FFFFFFFF,00000000,FFFFFFFF	; Set bit indicating RESET
 Exit    = 01000000,FFFFFFFF,00000000,FFFFFFFF	; Set bit indicating Exit 
 Coin    = 00000000,FFFFFFFF,00000000,FF7FFFFF

 Start   = 00000000,FFFFFF7F,00000080,FFFFFFFF	; Start game

#        	       	<rom name="qb3_le_t7.bin" size="8192" crc="adaaee4c" sha1="35c6bbb50646a3ddec12f115fcf3f2283e15b0a0" region="maincpu" offset="0"/>
#        	       	<rom name="qb3_lo_p7.bin" size="8192" crc="72f6199f" sha1="ae8f81f218940cfc3aef8f82dfe8cc14220770ce" region="maincpu" offset="1"/>
#        	       	<rom name="qb3_ue_u7.bin" size="8192" crc="050a996d" sha1="bf29236112746b5925b29fb231f152a4bde3f4f9" region="maincpu" offset="4000"/>
#        	       	<rom name="qb3_uo_r7.bin" size="8192" crc="33fa77a2" sha1="27a6853f8c2614a2abd7bfb9a62c357797312068" region="maincpu" offset="4001"/>
#        	       	<display tag="screen" type="vector" rotate="180" flipx="yes" refresh="38.000000" />
   */
#endif
}

void startFrame_tailgunner(void) {
#define TG_IO_START 0x80 /* for ioInputs */
#define TG_IO_SHIELDS 0x40
#define TG_IO_FIRE 0x20
#define TG_IO_DOWN 0x10
#define TG_IO_UP 0x08
#define TG_IO_LEFT 0x04
#define TG_IO_RIGHT 0x02
  //#define TG_IO_COIN    0x01
#define TG_SW_ABORT SW_ABORT /* for ioSwitches */
#define TG_SW_COIN 0x080
  // static int prevButtonState = 0;  // for debouncing

  frameCounter += 1;
  // DEBUG_OUT("v_WaitRecal(); v_setBrightness(64);v_readButtons();v_readJoystick1Analog(); // %d\n", frameCounter);

  // v_WaitRecal();
  // v_doSound();
  //v_readButtons ();		// update currentButtonState
  //v_readJoystick1Analog ();
  // v_playAllSFX();

  // default inactive:
  ioInputs = initialInputs | TG_IO_LEFT | TG_IO_RIGHT | TG_IO_UP | TG_IO_DOWN | TG_IO_START | TG_IO_SHIELDS | TG_IO_FIRE;
  ioSwitches = initialSwitches | TG_SW_COIN;
#ifdef VSTCM
  // Update the button objects
  button2.update();
  // middle button on PCB starts game
  if (button2.fell()) {
    // ioSwitches &= ~TG_SW_COIN;
    ioInputs &= ~TG_IO_START;  // needs 1 coin
  }
#endif
  /* if ((currentButtonState & ~prevButtonState) & VEC_BUTTON_1_1) ioSwitches &= ~TG_SW_COIN;	// only on rising edge
   prevButtonState = currentButtonState;

   // set x and y from joystick
   RCram[42] = JoyX = (currentJoy1X * 5 / 2) & 0xfff;	// crude but the best I've found
   RCram[43] = JoyY = (currentJoy1Y * 5 / 2) & 0xfff;   // WHY ARE THE JOYSTICKS NON-RESPONSIVE IN STANDALONE MODE???

   if (currentButtonState & VEC_BUTTON_1_2) ioInputs &= ~TG_IO_START;
   if (currentButtonState & VEC_BUTTON_1_3) ioInputs &= ~TG_IO_SHIELDS;
   if (currentButtonState & VEC_BUTTON_1_4) ioInputs &= ~TG_IO_FIRE;
   */
}

void startFrame_demon(void) {
#define DE_IO_P1START 0x01  // 1-player start
#define DE_IO_P1WALK 0x10
#define DE_IO_P1FIRE 0x20
#define DE_IO_P1LEFT 0x04
#define DE_IO_P1RIGHT 0x08
#define DE_IO_P1PANIC 0x0200

#define DE_IO_P2START 0x02  // 2-player start
#define DE_IO_P2WALK 0x2000
#define DE_IO_P2FIRE 0x4000
#define DE_IO_P2LEFT 0x0800
#define DE_IO_P2RIGHT 0x1000
#define DE_IO_P2PANIC 0x0400

#define DE_SW_ABORT SW_ABORT /* for ioSwitches */
#define DE_SW_COIN 0x080     // Not used in freeplay mode
  //static int prevButtonState=0;	// for debouncing
  frameCounter += 1;
  // DEBUG_OUT("v_WaitRecal(); v_setBrightness(64);v_readButtons();v_readJoystick1Analog(); // %d\n", frameCounter);

  // v_WaitRecal();
  // v_doSound();
  // v_readButtons();  // update currentButtonState
  //  v_readJoystick1Analog();
  //v_readJoystick2Analog ();  // NOT YET IMPLEMENTED.
  // v_playAllSFX();

  // Unfortunately, it's quite common to press LEFT and RIGHT simultaneously by accident with this
  // layout, and accidentally invoke the configuration screen.  Need to think about how we will
  // handle this...

  // default inactive:
  ioInputs = initialInputs | DE_IO_P1LEFT | DE_IO_P1RIGHT | DE_IO_P1START | DE_IO_P1WALK | DE_IO_P1FIRE | DE_IO_P1PANIC
             | DE_IO_P2LEFT | DE_IO_P2RIGHT | DE_IO_P2START | DE_IO_P2WALK | DE_IO_P2FIRE | DE_IO_P2PANIC;

  // ioSwitches |= DE_SW_COIN;
  ioSwitches = initialSwitches | 0;


  // not used in freeplay mode
  // if ((currentButtonState & ~prevButtonState) & VEC_BUTTON_1_1) ioSwitches &= ~DE_SW_COIN;	// only on rising edge

  // digital joysticks...
  /* if (currentJoy1X < -30) ioInputs &= ~DE_IO_P1LEFT;
   if (currentJoy1X > 30) ioInputs &= ~DE_IO_P1RIGHT;
   if (currentJoy1Y > 30) ioInputs &= ~DE_IO_P1WALK;
   if (currentJoy1Y < -30) ioInputs &= ~DE_IO_P1PANIC;

   if (currentJoy2X < -30) ioInputs &= ~DE_IO_P2LEFT;
   if (currentJoy2X > 30) ioInputs &= ~DE_IO_P2RIGHT;
   if (currentJoy2Y > 30) ioInputs &= ~DE_IO_P2WALK;
   if (currentJoy2Y < -30) ioInputs &= ~DE_IO_P2PANIC;

   if (currentButtonState & VEC_BUTTON_1_1) ioInputs &= ~DE_IO_P1START;
   if (currentButtonState & VEC_BUTTON_1_2) ioInputs &= ~DE_IO_P2START;

   if (currentButtonState & VEC_BUTTON_1_1) ioInputs &= ~DE_IO_P1LEFT;
   if (currentButtonState & VEC_BUTTON_1_2) ioInputs &= ~DE_IO_P1RIGHT;
   if (currentButtonState & VEC_BUTTON_1_3) ioInputs &= ~DE_IO_P1WALK;
   if (currentButtonState & VEC_BUTTON_1_4) ioInputs &= ~DE_IO_P1FIRE;

   if (currentButtonState & VEC_BUTTON_2_1) ioInputs &= ~DE_IO_P2LEFT;
   if (currentButtonState & VEC_BUTTON_2_2) ioInputs &= ~DE_IO_P2RIGHT;
   if (currentButtonState & VEC_BUTTON_2_3) ioInputs &= ~DE_IO_P2WALK;
   if (currentButtonState & VEC_BUTTON_2_4) ioInputs &= ~DE_IO_P2FIRE;
   prevButtonState = currentButtonState;*/
}

void startFrame_speedfreak(void) {
  static int isInit = 0;
  // static int coinKey = 0;
  //  static int startKey = 0;
  //  static int gasKey = 0;
  //  static int gear1Key = 0;
  //static int currentGear = -1;

  frameCounter += 1;
  // DEBUG_OUT("v_WaitRecal(); v_setBrightness(64);v_readButtons();v_readJoystick1Analog(); // %d\n", frameCounter);
  // v_WaitRecal();
  // v_doSound();
  // v_readButtons();
  // v_readJoystick1Analog();
  // v_playAllSFX();

  if (isInit == 0) {
    ioSwitches = initialSwitches | 0;
    ioInputs = initialInputs | 0xFFFF;
    isInit = 1;
  }

  // coin is button 1 joyport 0
  /*  if (currentButtonState & 1) {
    // Coin = 00000000,FFFFFFFF,00000000,FF7FFFFF
    if (!coinKey) {
      coinKey = 1;
      ioSwitches = ioSwitches | 0x0000;
      ioInputs = ioInputs | 0x0000;

      ioSwitches = ioSwitches & 0xffff;
      ioInputs = ioInputs & 0xffff;
    }
  } else {
    if (coinKey) {
      coinKey = 0;
      ioSwitches = ioSwitches | 0x0000;
      ioInputs = ioInputs | 0x0000;

      ioSwitches = ioSwitches & 0xff7f;
      ioInputs = ioInputs & 0xffff;
    }
  }

  // start is button 2 joyport 0
  if (currentButtonState & 2) {
    // Start = 00000000,FFFFFF7F,00000080,FFFFFFFF ; Start game
    if (!startKey) {
      startKey = 1;
      ioSwitches = ioSwitches | 0x0000;
      ioInputs = ioInputs | 0x0000;

      ioSwitches = ioSwitches & 0xffff;
      ioInputs = ioInputs & 0xFF7F;
    }
  } else {
    if (startKey) {
      startKey = 0;
      ioSwitches = ioSwitches | 0x0000;
      ioInputs = ioInputs | 0x0080;

      ioSwitches = ioSwitches & 0xffff;
      ioInputs = ioInputs & 0xffff;
    }
    //currentGear = -1;
  }

  // gas is button 4 joyport 0
  if (currentButtonState & 8) {
    // Gas = 00000000,FFFFFEFF,00000100,FFFFFFFF ; Gas
    if (!gasKey) {
      gasKey = 1;
      ioInputs = ioInputs & 0xFEFF;
    }
  } else {
    if (gasKey) {
      gasKey = 0;
      ioInputs = ioInputs | 0x0100;
    }
  }

  // gear 1 is button 3 joyport 0
  if (currentButtonState & 4) {
    // Gear1 = 000000E0,FFFFFFEF,00000000,FFFFFFFF ; First Gear
    if (!gear1Key) {
      gear1Key = 1;
      ioInputs = ioInputs | 0x00E0;
      ioInputs = ioInputs & 0xFFEF;
    }
  } else {
    if (gear1Key) {
      gear1Key = 0;
    }
  }

  // bit 0 indicates 0 =  negative/ right
  // bit 0 indicates 1 =  positive/ left
  // bit 1-3 indicate speed in the direction
  // so min speed = 001, max = 111 -> 1-7

  if ((currentJoy1X > 0) && (currentJoy1X > 30)) {
    // range from 30-127 -> 0-97 / 16 -> 0-6 (+1)
    // left test
    ioInputs = ioInputs & 0xfff0;
    ioInputs = ioInputs | (((((currentJoy1X - 30) / 16) + 1) << 1) + 1); // between 1-7



    int j = ABS(currentJoy1X - 30) / 12 + 1;  // 0 - 97
    ioInputs = ioInputs & 0xfff0;
    ioInputs = ioInputs | ((j << 1) + 1); // between 1-7


  } else if ((currentJoy1X < 0) && (currentJoy1X < -30)) {
    // right test
    ioInputs = ioInputs & 0xfff0;
    ioInputs = ioInputs | (((((-currentJoy1X) - 30) / 16) + 1) << 1); // between 1-7 

    int j = ABS(currentJoy1X - 30) / 12 + 1;  // 0 - 97
    ioInputs = ioInputs & 0xfff0;
    ioInputs = ioInputs | (j << 1); // between 1-7 


  } else {
    // release should not be necessary, shift is cleared each round!
    ioInputs = ioInputs & 0xfff0;
  }*/
}

void startFrame(void) {
  switch (Game) {
    case GAME_RIPOFF:
      startFrame_ripoff();
      return;
    case GAME_SPACEWARS:
      startFrame_spacewars();
      return;
    case GAME_BOXINGBUGS:
      startFrame_boxingbugs();
      return;
    case GAME_ARMORATTACK:
      startFrame_armorattack();
      return;
    case GAME_STARCASTLE:
      startFrame_starcastle();
      return;
    case GAME_STARHAWK:
      startFrame_starhawk();
      return;
    case GAME_SOLARQUEST:
      startFrame_solarquest();
      return;
    case GAME_COSMICCHASM:
      startFrame_cosmicchasm();
      return;
    case GAME_WAROFTHEWORLDS:
      startFrame_waroftheworlds();
      return;
    case GAME_WARRIOR:
      startFrame_warrior();
      return;
    case GAME_BARRIER:
      startFrame_barrier();
      return;
    case GAME_SUNDANCE:
      startFrame_sundance();
      return;
    case GAME_QB3:
      startFrame_qb3();
      return;
    case GAME_TAILGUNNER:
      startFrame_tailgunner();  // Tailgunner calls the instruction that we use to determine vsync twice in a row without intervening drawing code.
      return;
    case GAME_DEMON:
      startFrame_demon();  // Demon calls the instruction that we use to determine vsync twice in a row without intervening drawing code.
      return;
    case GAME_SPEEDFREAK:
      startFrame_speedfreak();  // Speedfreak calls the instruction that we use to determine vsync twice in a row without intervening drawing code.
      return;
    default:
      // fprintf(stderr, "Game %d not defined!\n", Game);
      strcpy(gMsg, "Game not defined!");
      return;  // added this just to get it to compile
  }
}

void CinemaVectorData(int RCFromX, int RCFromY, int RCToX, int RCToY, int vgColour) {
  RCFromX = SEX(RCFromX);
  RCFromY = SEX(RCFromY);
  RCToX = SEX(RCToX);
  RCToY = SEX(RCToY);
  line(RCFromX, RCFromY, RCToX, RCToY, vgColour);
}

void xUNFINISHED(const char *s, int RCregister_PC) {
  // DEBUG_OUT("%04x DANGER: Unimplemented instruction - %s\n", RCregister_PC, s);
  exit(1);
}
#define UNFINISHED(s) xUNFINISHED(s, RCregister_PC)

/* Reset C-CPU registers, flags, etc to default starting values */
void cineReset(void) {

  /* zero registers */
  RCregister_PC = 0;
  RCregister_A = 0;
  RCregister_B = 0;
  RCregister_I = 0;
  RCregister_J = 0;
  RCregister_P = 0;
  RCFromX = 0;
  RCFromY = 0;
  RCregister_T = 0;

  /* zero flags */
  RCflag_C = 0;

  /* reset RCstate */
  RCstate = (RCCINESTATE)0;

  /* reset RCram */
  memset(RCram, 0, sizeof(RCram));

  /* reset internal RCstate */
  RCcmp_old = 0;
  RCcmp_new = 0;
  SETA0(0);
}

void cineSetGame(const char *name, int id) {
  strcpy(ccpu_game_name, name);
  ccpu_game_id = id;
}

void cineSetJMI(UINT8 j) {
  ccpu_jmi_dip = j;
  // DEBUG_OUT("cineSetJMI(%u);\n", j);
}

void cineSetMSize(UINT8 m) {
  ccpu_msize = m;
  // DEBUG_OUT("cineSetMSize(%u);\n", m);
}

void cineSetMonitor(UINT8 m) {
  ccpu_monitor = m;
  // DEBUG_OUT("cineSetMonitor(%u);\n", m);
}
/*
UINT32 cineGetElapsedTicks(UINT32 dwClearIt) {
  UINT32 dwTemp;
  dwTemp = dwElapsedTicks;
  if (dwClearIt) dwElapsedTicks = 0;
  return (dwTemp);
}
*/
void cineReleaseTimeslice(void) {
  bBailOut = true;
}

/* extra functions */

//#include "cinedbg.i"

/* ----------------------------------------------- Trace debugger cinedbg.c */

/* handy macros */

void disassemble(char *buffer, unsigned int maxlen, unsigned int address);

#define START(x) DEBUG_OUT("Entered C-CPU function: %s\n", x)
#define STOP(x) DEBUG_OUT("Left C-CPU function: %s\n", x)

/* opcode tables for debugging */
typedef enum {
  CLR,
  LDA,
  INP,
  ADD,
  SUB,
  LDJ,
  LDP,
  OUT,
  CMP,
  LDI,
  STA,
  VIN,
  VDR,
  XLT,
  MUL,
  LLT,
  WAI,
  AWD,
  AND,
  LSR,
  LSL,
  ASR,
  ASRD,
  LSLD,
  JPPB,
  JMIB,
  JDRB,
  JLTB,
  JEQB,
  JNCB,
  JAOB,
  NOPB,
  JMPA,
  JMIA,
  JDRA,
  JLTA,
  JEQA,
  JNCA,
  JAOA,
  NOPA,
  JEIA,
  JEIB
} opcode_mnemonics;

typedef struct
{
  opcode_mnemonics od_opcode;
  const char *od_name;
} opcode_detail;

const opcode_detail opcodes[] = {
  { CLR, "clr" },
  { LDA, "lda" },
  { INP, "inp" },
  { ADD, "add" },
  { SUB, "sub" },
  { LDJ, "ldj" },
  { LDP, "ldp" },
  { OUT, "out" },
  { CMP, "cmp" },
  { LDI, "ldi" },
  { STA, "sta" },
  { VIN, "vin" },
  { VDR, "vdr" },
  { XLT, "xlt" },
  { MUL, "mul" },
  { LLT, "llt" },
  { WAI, "wai" },
  { AWD, "awd" },
  { AND, "and" },
  { LSR, "lsr" },
  { LSL, "lsl" },
  { ASR, "asr" },
  { ASRD, "asrd" },
  { LSLD, "lsld" },
  { JPPB, "jppb" },
  { JMIB, "jmib" },
  { JDRB, "jdrb" },
  { JLTB, "jltb" },
  { JEQB, "jeqb" },
  { JNCB, "jncb" },
  { JAOB, "jaob" },
  { NOPB, "nopb" },
  { JMPA, "jmpa" },
  { JMIA, "jmia" },
  { JDRA, "jdra" },
  { JLTA, "jlta" },
  { JEQA, "jeqa" },
  { JNCA, "jnca" },
  { JAOA, "jaoa" },
  { NOPA, "nopa" },
  { JEIA, "jeia" },
  { JEIB, "jeib" }
};

typedef enum {
  ACC,    /* Accumulator */
  ADIR,   /* Acc Direct memory access */
  AIM4,   /* Acc 4 bit immediate */
  AIM4X,  /* Acc 4 bit immediate extended size */
  AIM8,   /* Acc 8 bit immediate */
  AINDM,  /* Acc indirect through memory */
  AIMX,   /* Acc immediate extended A-reg */
  AXLT,   /* Acc lookup ROM using Acc as pointer */
  AIRG,   /* Acc Through the I-reg */
  IRG,    /* Through the I-reg */
  IM4,    /* 4 bit immediate */
  IM12,   /* 12 bit immediate */
  DIRECT, /* Direct memory access */
  IMP,    /* Implied */
  JUMP,   /* Acc selection/Jump instruction */
  JUMPX   /* Acc selection/Extended jump instruction */
} amode_mnemonics;

typedef struct
{
  amode_mnemonics ad_amode;
  const char *ad_name;
} amode_detail;

amode_detail amodes[] = {
  { ACC, "acc" },
  { ADIR, "adir" },
  { AIM4, "aim4" },
  { AIM4X, "aim4x" },
  { AIM8, "aim8" },
  { AINDM, "aindm" },
  { AIMX, "aimx" },
  { AXLT, "axlt" },
  { AIRG, "airg" },
  { IRG, "irg" },
  { IM4, "im4" },
  { IM12, "im12" },
  { DIRECT, "dir" },
  { IMP, "imp" },
  { JUMP, "jump" },
  { JUMPX, "jumpx" }
};

typedef struct
{
  opcode_mnemonics ot_opcode;
  amode_mnemonics ot_amode;
} opcode_table_entry;

opcode_table_entry opcode_table[] = {
  { CLR, ACC },   /* 00 */
  { LDA, AIM4X }, /* 01 */
  { LDA, AIM4X }, /* 02 */
  { LDA, AIM4X }, /* 03 */
  { LDA, AIM4X }, /* 04 */
  { LDA, AIM4X }, /* 05 */
  { LDA, AIM4X }, /* 06 */
  { LDA, AIM4X }, /* 07 */
  { LDA, AIM4X }, /* 08 */
  { LDA, AIM4X }, /* 09 */
  { LDA, AIM4X }, /* 0A */
  { LDA, AIM4X }, /* 0B */
  { LDA, AIM4X }, /* 0C */
  { LDA, AIM4X }, /* 0D */
  { LDA, AIM4X }, /* 0E */
  { LDA, AIM4X }, /* 0F */

  { INP, ADIR }, /* 10 */
  { INP, ADIR }, /* 11 */
  { INP, ADIR }, /* 12 */
  { INP, ADIR }, /* 13 */
  { INP, ADIR }, /* 14 */
  { INP, ADIR }, /* 15 */
  { INP, ADIR }, /* 16 */
  { INP, ADIR }, /* 17 */
  { INP, ADIR }, /* 18 */
  { INP, ADIR }, /* 19 */
  { INP, ADIR }, /* 1A */
  { INP, ADIR }, /* 1B */
  { INP, ADIR }, /* 1C */
  { INP, ADIR }, /* 1D */
  { INP, ADIR }, /* 1E */
  { INP, ADIR }, /* 1F */

  { ADD, AIM8 }, /* 20 */
  { ADD, AIM4 }, /* 21 */
  { ADD, AIM4 }, /* 22 */
  { ADD, AIM4 }, /* 23 */
  { ADD, AIM4 }, /* 24 */
  { ADD, AIM4 }, /* 25 */
  { ADD, AIM4 }, /* 26 */
  { ADD, AIM4 }, /* 27 */
  { ADD, AIM4 }, /* 28 */
  { ADD, AIM4 }, /* 29 */
  { ADD, AIM4 }, /* 2A */
  { ADD, AIM4 }, /* 2B */
  { ADD, AIM4 }, /* 2C */
  { ADD, AIM4 }, /* 2D */
  { ADD, AIM4 }, /* 2E */
  { ADD, AIM4 }, /* 2F */

  { SUB, AIM8 }, /* 30 */
  { SUB, AIM4 }, /* 31 */
  { SUB, AIM4 }, /* 32 */
  { SUB, AIM4 }, /* 33 */
  { SUB, AIM4 }, /* 34 */
  { SUB, AIM4 }, /* 35 */
  { SUB, AIM4 }, /* 36 */
  { SUB, AIM4 }, /* 37 */
  { SUB, AIM4 }, /* 38 */
  { SUB, AIM4 }, /* 39 */
  { SUB, AIM4 }, /* 3A */
  { SUB, AIM4 }, /* 3B */
  { SUB, AIM4 }, /* 3C */
  { SUB, AIM4 }, /* 3D */
  { SUB, AIM4 }, /* 3E */
  { SUB, AIM4 }, /* 3F */

  { LDJ, IM12 }, /* 40 */
  { LDJ, IM12 }, /* 41 */
  { LDJ, IM12 }, /* 42 */
  { LDJ, IM12 }, /* 43 */
  { LDJ, IM12 }, /* 44 */
  { LDJ, IM12 }, /* 45 */
  { LDJ, IM12 }, /* 46 */
  { LDJ, IM12 }, /* 47 */
  { LDJ, IM12 }, /* 48 */
  { LDJ, IM12 }, /* 49 */
  { LDJ, IM12 }, /* 4A */
  { LDJ, IM12 }, /* 4B */
  { LDJ, IM12 }, /* 4C */
  { LDJ, IM12 }, /* 4D */
  { LDJ, IM12 }, /* 4E */
  { LDJ, IM12 }, /* 4F */

  { JPPB, JUMP }, /* 50 */
  { JMIB, JUMP }, /* 51 */
  { JDRB, JUMP }, /* 52 */
  { JLTB, JUMP }, /* 53 */
  { JEQB, JUMP }, /* 54 */
  { JNCB, JUMP }, /* 55 */
  { JAOB, JUMP }, /* 56 */
  { NOPB, IMP },  /* 57 */

  { JMPA, JUMP }, /* 58 */
  { JMIA, JUMP }, /* 59 */
  { JDRA, JUMP }, /* 5A */
  { JLTA, JUMP }, /* 5B */
  { JEQA, JUMP }, /* 5C */
  { JNCA, JUMP }, /* 5D */
  { JAOA, JUMP }, /* 5E */
  { NOPA, IMP },  /* 5F */

  { ADD, ADIR }, /* 60 */
  { ADD, ADIR }, /* 61 */
  { ADD, ADIR }, /* 62 */
  { ADD, ADIR }, /* 63 */
  { ADD, ADIR }, /* 64 */
  { ADD, ADIR }, /* 65 */
  { ADD, ADIR }, /* 66 */
  { ADD, ADIR }, /* 67 */
  { ADD, ADIR }, /* 68 */
  { ADD, ADIR }, /* 69 */
  { ADD, ADIR }, /* 6A */
  { ADD, ADIR }, /* 6B */
  { ADD, ADIR }, /* 6C */
  { ADD, ADIR }, /* 6D */
  { ADD, ADIR }, /* 6E */
  { ADD, ADIR }, /* 6F */

  { SUB, ADIR }, /* 70 */
  { SUB, ADIR }, /* 71 */
  { SUB, ADIR }, /* 72 */
  { SUB, ADIR }, /* 73 */
  { SUB, ADIR }, /* 74 */
  { SUB, ADIR }, /* 75 */
  { SUB, ADIR }, /* 76 */
  { SUB, ADIR }, /* 77 */
  { SUB, ADIR }, /* 78 */
  { SUB, ADIR }, /* 79 */
  { SUB, ADIR }, /* 7A */
  { SUB, ADIR }, /* 7B */
  { SUB, ADIR }, /* 7C */
  { SUB, ADIR }, /* 7D */
  { SUB, ADIR }, /* 7E */
  { SUB, ADIR }, /* 7F */

  { LDP, IM4 }, /* 80 */
  { LDP, IM4 }, /* 81 */
  { LDP, IM4 }, /* 82 */
  { LDP, IM4 }, /* 83 */
  { LDP, IM4 }, /* 84 */
  { LDP, IM4 }, /* 85 */
  { LDP, IM4 }, /* 86 */
  { LDP, IM4 }, /* 87 */
  { LDP, IM4 }, /* 88 */
  { LDP, IM4 }, /* 89 */
  { LDP, IM4 }, /* 8A */
  { LDP, IM4 }, /* 8B */
  { LDP, IM4 }, /* 8C */
  { LDP, IM4 }, /* 8D */
  { LDP, IM4 }, /* 8E */
  { LDP, IM4 }, /* 8F */

  { OUT, ADIR }, /* 90 */
  { OUT, ADIR }, /* 91 */
  { OUT, ADIR }, /* 92 */
  { OUT, ADIR }, /* 93 */
  { OUT, ADIR }, /* 94 */
  { OUT, ADIR }, /* 95 */
  { OUT, ADIR }, /* 96 */
  { OUT, ADIR }, /* 97 */
  { OUT, ADIR }, /* 98 */
  { OUT, ADIR }, /* 99 */
  { OUT, ADIR }, /* 9A */
  { OUT, ADIR }, /* 9B */
  { OUT, ADIR }, /* 9C */
  { OUT, ADIR }, /* 9D */
  { OUT, ADIR }, /* 9E */
  { OUT, ADIR }, /* 9F */

  { LDA, ADIR }, /* A0 */
  { LDA, ADIR }, /* A1 */
  { LDA, ADIR }, /* A2 */
  { LDA, ADIR }, /* A3 */
  { LDA, ADIR }, /* A4 */
  { LDA, ADIR }, /* A5 */
  { LDA, ADIR }, /* A6 */
  { LDA, ADIR }, /* A7 */
  { LDA, ADIR }, /* A8 */
  { LDA, ADIR }, /* A9 */
  { LDA, ADIR }, /* AA */
  { LDA, ADIR }, /* AB */
  { LDA, ADIR }, /* AC */
  { LDA, ADIR }, /* AD */
  { LDA, ADIR }, /* AE */
  { LDA, ADIR }, /* AF */

  { CMP, ADIR }, /* B0 */
  { CMP, ADIR }, /* B1 */
  { CMP, ADIR }, /* B2 */
  { CMP, ADIR }, /* B3 */
  { CMP, ADIR }, /* B4 */
  { CMP, ADIR }, /* B5 */
  { CMP, ADIR }, /* B6 */
  { CMP, ADIR }, /* B7 */
  { CMP, ADIR }, /* B8 */
  { CMP, ADIR }, /* B9 */
  { CMP, ADIR }, /* BA */
  { CMP, ADIR }, /* BB */
  { CMP, ADIR }, /* BC */
  { CMP, ADIR }, /* BD */
  { CMP, ADIR }, /* BE */
  { CMP, ADIR }, /* BF */

  { LDI, DIRECT }, /* C0 */
  { LDI, DIRECT }, /* C1 */
  { LDI, DIRECT }, /* C2 */
  { LDI, DIRECT }, /* C3 */
  { LDI, DIRECT }, /* C4 */
  { LDI, DIRECT }, /* C5 */
  { LDI, DIRECT }, /* C6 */
  { LDI, DIRECT }, /* C7 */
  { LDI, DIRECT }, /* C8 */
  { LDI, DIRECT }, /* C9 */
  { LDI, DIRECT }, /* CA */
  { LDI, DIRECT }, /* CB */
  { LDI, DIRECT }, /* CC */
  { LDI, DIRECT }, /* CD */
  { LDI, DIRECT }, /* CE */
  { LDI, DIRECT }, /* CF */

  { STA, ADIR }, /* D0 */
  { STA, ADIR }, /* D1 */
  { STA, ADIR }, /* D2 */
  { STA, ADIR }, /* D3 */
  { STA, ADIR }, /* D4 */
  { STA, ADIR }, /* D5 */
  { STA, ADIR }, /* D6 */
  { STA, ADIR }, /* D7 */
  { STA, ADIR }, /* D8 */
  { STA, ADIR }, /* D9 */
  { STA, ADIR }, /* DA */
  { STA, ADIR }, /* DB */
  { STA, ADIR }, /* DC */
  { STA, ADIR }, /* DD */
  { STA, ADIR }, /* DE */
  { STA, ADIR }, /* DF */

  { VDR, IMP },  /* E0 */
  { LDJ, IRG },  /* E1 */
  { XLT, AXLT }, /* E2 */
  { MUL, IRG },  /* E3 */
  { LLT, IMP },  /* E4 */
  { WAI, IMP },  /* E5 */
  { STA, AIRG }, /* E6 */
  { ADD, AIRG }, /* E7 */
  { SUB, AIRG }, /* E8 */
  { AND, AIRG }, /* E9 */
  { LDA, AIRG }, /* EA */
  { LSR, ACC },  /* EB */
  { LSL, ACC },  /* EC */
  { ASR, ACC },  /* ED */
  { ASRD, IMP }, /* EE */
  { LSLD, IMP }, /* EF */

  { VIN, IMP },  /* F0 */
  { LDJ, IRG },  /* F1 */
  { XLT, AXLT }, /* F2 */
  { MUL, IRG },  /* F3 */
  { LLT, IMP },  /* F4 */
  { WAI, IMP },  /* F5 */
  { STA, AIRG }, /* F6 */
  { AWD, AIRG }, /* F7 */
  { SUB, AIRG }, /* F8 */
  { AND, AIRG }, /* F9 */
  { LDA, AIRG }, /* FA */
  { LSR, ACC },  /* FB */
  { LSL, ACC },  /* FC */
  { ASR, ACC },  /* FD */
  { ASRD, IMP }, /* FE */
  { LSLD, IMP }  /* FF */
};

/* disassemble() appends a disassembly of the specified address to
 * the end of the specified text buffer. */
void disassemble(char *buffer, unsigned int maxlen, unsigned int address) {
  char ambuffer[40]; /* text buffer for addressing mode values */
  char opbuffer[40]; /* text buffer for opcodes etc. */
  char flbuffer[80]; /* text buffer for flag dump */
  RCCINEBYTE opcode;
  RCCINEBYTE opsize = 1;
  int iter = 0;

  /* which opcode in opcode table? (includes immediate data) */
  opcode = rom[address];

  /* build addressing mode (value to opcode) */

  memset(ambuffer, 0, sizeof(ambuffer));
  switch (amodes[opcode_table[opcode].ot_amode].ad_amode) {

      /* 4-bit immediate value */
    case AIM4:
    case IM4:
      sprintf(ambuffer, "#$%X", opcode & 0x0F);
      break;

      /* 4-bit extended immediate value */
    case AIM4X:
      sprintf(ambuffer, "#$%X", (opcode & 0x0F) << 8);
      break;

      /* 8-bit immediate value */
    case AIM8:
      sprintf(ambuffer, "#$%02X", rom[address + 1]);
      opsize++; /* required second byte for value */
      break;

      /* [m] -- indirect through memory */
    case AINDM:
      sprintf(ambuffer, "AINDM/Error");
      break;

      /* [i] -- indirect through 'I' */
    case AIRG:
    case IRG:
      sprintf(ambuffer, "[i]");
      break;

      /* extended 12-bit immediate value */
    case AIMX:
      sprintf(ambuffer, "AIMX/Error");
      break;

      /* no special params */
    case ACC:
    case AXLT:
    case IMP:
      ambuffer[0] = '\0';
      break;

      /* 12-bit immediate value */
    case IM12:
      sprintf(ambuffer, "#$%03X",
              (rom[address] & 0x0F) + (rom[address + 1] & 0xF0) + ((rom[address + 1] & 0x0F) << 8));
      opsize++;
      break;

      /* display address of direct addressing modes */
    case ADIR:
    case DIRECT:
      sprintf(ambuffer, "$%X", opcode & 0x0F);
      break;

      /* jump through J register */
    case JUMP:
      sprintf(ambuffer, "<jump>");
      break;

      /* extended jump */
    case JUMPX:
      sprintf(ambuffer, "JUMPX/Error");
      break;

  } /* switch on addressing mode */

  /* build flags dump */
  sprintf(flbuffer, "A=%03X B=%03X I=%03XZ J=%03X P=%X "
                    "A0=%02X %02X N%X O%X %c%c%c%c",
          RCregister_A, RCregister_B, RCregister_I /* << 1 */, /* use the <<1 for Zonn style */
          RCregister_J, RCregister_P, GETA0(), GETFC() /* ? 'C' : 'c' */,
          RCcmp_new, RCcmp_old,
          ((RCstate == RCstate_A) || (RCstate == RCstate_AA)) ? 'A' : ' ',
          (RCstate == RCstate_AA) ? 'A' : ' ',
          ((RCstate == RCstate_B) || (RCstate == RCstate_BB)) ? 'B' : ' ',
          (RCstate == RCstate_BB) ? 'B' : ' ');

  /* build the final output string. Format is as follows: ADDRESS: OPCODE-ROM-DUMP\tOPCODE VALUE\tFLAGS */

  /* append complete opcode ROM dump */
  memset(opbuffer, 0, sizeof(opbuffer));
  for (iter = 0; iter < opsize; iter++) {
    sprintf(opbuffer + (iter * 3), " %02X", rom[address + iter]);
  }

  /* create final output */
  sprintf(buffer, "%04X:%-6s : %-4s %-6s : %s",
          address, opbuffer,
          opcodes[opcode_table[opcode].ot_opcode].od_name,
          ambuffer, flbuffer);

  return;
}
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
