english1234/vstcm/Vector Kong Teensy MAME/common.c

#include "WProgram.h"
/*********************************************************************
  common.c

  Generic functions, mostly ROM and graphics related.
  NO LONGER TRUE! Filled up with VSTCM and Vector Donkey Kong specific 
  routines adapted and/or written by Robin Champion / November 2022
*********************************************************************/

#include <arduino.h>
#include <math.h>
#include "driver.h"
#include "myport.h"

/* These globals are only kept on a machine basis - LBO 042898 */
extern unsigned int dispensed_tickets;
unsigned int coins[COIN_COUNTERS];
unsigned int lastcoin[COIN_COUNTERS];
unsigned int coinlockedout[COIN_COUNTERS];

/* LBO */
#ifdef LSB_FIRST
#define intelLong(x) (x)
#define BL0 0
#define BL1 1
#define BL2 2
#define BL3 3
#define WL0 0
#define WL1 1
#else
#define intelLong(x) (((x << 24) | (((unsigned long)x) >> 24) | ((x & 0x0000ff00) << 8) | ((x & 0x00ff0000) >> 8)))
#define BL0 3
#define BL1 2
#define BL2 1
#define BL3 0
#define WL0 1
#define WL1 0
#endif

#define TA

#define read_dword(address) *(int *)address
#define write_dword(address, data) *(int *)address = data

// VSTCM Vector Kong specific routines

extern void draw_to_xy(int, int);
extern int cpu_readmem16(int address);
extern void cpu_writemem29_dword(int address, int data);
extern void cpu_writemem16(int address, int data);

// Local function prototypes
uint8_t read_u8(int);
uint32_t read_direct_u32(int);

// Basic vector drawing functions
// 12 for X, 15 for Y work well
// add 700 for X, 0 for Y

#define X_SCALE_FACTOR 12
#define Y_SCALE_FACTOR 15
#define X_ADD 700
#define Y_ADD 0

#define GW 9  // girder width, to make it easy to increase if gaps appear on screen between tiles
#define GH 9  // girder width

// Defining region codes
#define LEFT 0x1
#define RIGHT 0x2
#define BOTTOM 0x4
#define TOP 0x8

#define BLK 0xF00
#define WHT 0xF01
#define YEL 0xF02
#define RED 0xF03
#define BLU 0xF04
#define MBR 0xF05
#define BRN 0xF06
#define MAG 0xF07
#define PNK 0xF08
#define LBR 0xF09
#define CYN 0xF0A
#define GRY 0xF0B
#define BRIGHT_BLUE 0xF0C
#define LAST_POINT 0xF0D
#define BR 0xF0E   // instruction to break in a vector chain
#define GRN 0xF0F  // Green (not normally needed)

#define MODE 0x600a
#define STAGE 0x6227
#define LEVEL 0x6229
#define VRAM_BL 0x77bf
#define VRAM_TR 0x7440

typedef struct Chunk {
  struct Chunk *nextChunk;
  uint16_t x0;  // We'll just use 12 bits of X & Y for a 4096 point resolution
  uint16_t y0;
  uint16_t x1;  // We'll just use 12 bits of X & Y for a 4096 point resolution
  uint16_t y1;
  uint8_t r;  // Max value of each colour is 255
  uint8_t g;
  uint8_t b;
} DataChunk_t;

#define MAX_PTS 4000  // Peaks around 2750

static int vector_color;
static int game_mode, last_mode;
static int _growling;
static int frame_count;
static uint16_t s_in_vec_cnt;
static uint16_t s_tmp_vec_cnt;
static float s_in_vec_last_x;
static float s_in_vec_last_y;
static uint32_t s_out_vec_cnt;
static DataChunk_t *s_in_vec_list;
static DataChunk_t *s_out_vec_list;
static DataChunk_t *s_tmp_vec_list;
static int32_t s_clipx_min = 1;
static int32_t s_clipx_max = 4095;
static int32_t s_clipy_min = 1;
static int32_t s_clipy_max = 4095;

typedef struct {
  const uint16_t points[270];  // maximum 270 points per vector
} dk_sprite_t;

// Vector library
dk_sprite_t vector_library[] = {
  [0x00] = { 0, 2, 0, 4, 2, 6, 4, 6, 6, 4, 6, 2, 4, 0, 2, 0, 0, 2, LAST_POINT },                            // 0                                                                                                                                                                                                                                                                              // 0
  [0x01] = { 0, 0, 0, 6, 0, 3, 6, 3, 5, 1, LAST_POINT },                                                    // 1 optimised without breaks                                                                                                                                                                                                                                                                                                   // 1                                                                                                                                                                                                                                                                              // 1
  [0x02] = { 0, 6, 0, 0, 5, 6, 6, 3, 5, 0, LAST_POINT },                                                    // 2                                                                                                                                                                                                                                                                              // 2
  [0x03] = { 1, 0, 0, 1, 0, 5, 1, 6, 2, 6, 3, 5, 3, 2, 6, 6, 6, 1, LAST_POINT },                            // 3                                                                                                                                                                                                                                                                              // 3
  [0x04] = { 0, 5, 6, 5, 2, 0, 2, 7, LAST_POINT },                                                          // 4                                                                                                                                                                                                                                                                              // 4
  [0x05] = { 1, 0, 0, 1, 0, 5, 2, 6, 4, 5, 4, 0, 6, 0, 6, 5, LAST_POINT },                                  // 5                                                                                                                                                                                                                                                                              // 5
  [0x06] = { 3, 0, 1, 0, 0, 1, 0, 5, 1, 6, 2, 6, 3, 5, 3, 0, 6, 2, 6, 5, LAST_POINT },                      // 6                                                                                                                                                                                                                                                                              // 6
  [0x07] = { 6, 0, 6, 6, 0, 2, LAST_POINT },                                                                // 7                                                                                                                                                                                                                                                                              // 7
  [0x08] = { 2, 0, 0, 1, 0, 5, 2, 6, 5, 0, 6, 1, 6, 4, 5, 5, 2, 0, LAST_POINT },                            // 8                                                                                                                                                                                                                                                                              // 8
  [0x09] = { 0, 1, 0, 4, 2, 6, 5, 6, 6, 5, 6, 1, 5, 0, 4, 0, 3, 1, 3, 6, LAST_POINT },                      // 9                                                                                                                                                                                                                                                                              // 9
  [0x10] = { LAST_POINT },                                                                                  // space                                                                                                                                                                                                                                                                                                                                   // space
  [0x11] = { 0, 0, 4, 0, 6, 3, 4, 6, 0, 6, 2, 6, 2, 0, LAST_POINT },                                        // A                                                                                                                                                                                                                                                                                    // A
  [0x12] = { 0, 0, 6, 0, 6, 5, 5, 6, 4, 6, 3, 5, 2, 6, 1, 6, 0, 5, 0, 0, BR, BR, 3, 0, 3, 5, LAST_POINT },  // B
  [0x13] = { 1, 6, 0, 5, 0, 2, 2, 0, 4, 0, 6, 2, 6, 5, 5, 6, LAST_POINT },                                  // C
  [0x14] = { 0, 0, 6, 0, 6, 4, 4, 6, 2, 6, 0, 4, 0, 0, LAST_POINT },                                        // D
  [0x15] = { 0, 5, 0, 0, 3, 0, 3, 4, 3, 0, 6, 0, 6, 5, LAST_POINT },                                        // E                                                                                                                                                                                                                                                                                     // E optimised with no breaks                                                                                                                                                                                                                                                                                      // E
  [0x16] = { 0, 0, 3, 0, 3, 5, 3, 0, 6, 0, 6, 6, LAST_POINT },                                              // F optimised without breaks
  [0x17] = { 3, 4, 3, 6, 0, 6, 0, 2, 2, 0, 4, 0, 6, 2, 6, 6, LAST_POINT },                                  // G
  [0x18] = { 0, 0, 6, 0, 3, 0, 3, 6, 0, 6, 6, 6, LAST_POINT },                                              // H optimised without breaks                                                                                                                                                                                                                                                                                     // H
  [0x19] = { 0, 0, 0, 6, 0, 3, 6, 3, 6, 0, 6, 6, LAST_POINT },                                              // I optimised to remove break                                                                                                                                                                                                                                                                                // I
  [0x1a] = { 1, 0, 0, 1, 0, 5, 1, 6, 6, 6, LAST_POINT },                                                    // J
  [0x1b] = { 0, 6, 3, 0, 6, 6, 3, 0, 0, 0, 6, 0, LAST_POINT },                                              // K optimised without breaks                                                                                                                                                                                                                                                                           // K
  [0x1c] = { 6, 0, 0, 0, 0, 5, LAST_POINT },                                                                // L
  [0x1d] = { 0, 0, 6, 0, 2, 3, 6, 6, 0, 6, LAST_POINT },                                                    // M
  [0x1e] = { 0, 0, 6, 0, 0, 6, 6, 6, LAST_POINT },                                                          // N
  [0x1f] = { 1, 0, 5, 0, 6, 1, 6, 5, 5, 6, 1, 6, 0, 5, 0, 1, 1, 0, LAST_POINT },                            // O
  [0x20] = { 0, 0, 6, 0, 6, 5, 5, 6, 3, 6, 2, 5, 2, 0, LAST_POINT },                                        // P
  [0x21] = { 1, 0, 5, 0, 6, 1, 6, 5, 5, 6, 2, 6, 0, 4, 0, 1, 1, 0, BR, BR, 0, 6, 2, 3, LAST_POINT },        // Q
  [0x22] = { 0, 0, 6, 0, 6, 5, 5, 6, 4, 6, 2, 3, 2, 0, 2, 3, 0, 6, LAST_POINT },                            // R
  [0x23] = { 1, 0, 0, 1, 0, 5, 1, 6, 2, 6, 4, 0, 5, 0, 6, 1, 6, 4, 5, 5, LAST_POINT },                      // S
  [0x24] = { 6, 0, 6, 6, 6, 3, 0, 3, LAST_POINT },                                                          // T optimised to remove break                                                                                                                                                                                                                                                                                                           // T
  [0x25] = { 6, 0, 1, 0, 0, 1, 0, 5, 1, 6, 6, 6, LAST_POINT },                                              // U
  [0x26] = { 6, 0, 3, 0, 0, 3, 3, 6, 6, 6, LAST_POINT },                                                    // V
  [0x27] = { 6, 0, 2, 0, 0, 1, 4, 3, 0, 5, 2, 6, 6, 6, LAST_POINT },                                        // W
  [0x28] = { 0, 0, 6, 6, 3, 3, 6, 0, 0, 6, LAST_POINT },                                                    // X
  [0x29] = { 6, 0, 3, 3, 6, 6, 3, 3, 0, 3, LAST_POINT },                                                    // Y optimised to remove break
  [0x2a] = { 6, 0, 6, 6, 0, 0, 0, 6, LAST_POINT },                                                          // Z
  [0x2b] = { 0, 0, 1, 0, 1, 1, 0, 1, 0, 0, LAST_POINT },                                                    // dot
  [0x2c] = { 3, 0, 3, 5, LAST_POINT },                                                                      // dash
  [0x2d] = { 5, 0, 5, 6, LAST_POINT },                                                                      // underscore
  [0x2e] = { 4, 3, 4, 3, BR, BR, 2, 3, 2, 3, LAST_POINT },                                                  // colon
  [0x2f] = { 5, 0, 5, 6, LAST_POINT },                                                                      // Alt underscore
  [0x30] = { 0, 2, 2, 0, 4, 0, 6, 2, LAST_POINT },                                                          // Left bracket
  [0x31] = { 0, 2, 2, 4, 4, 4, 6, 2, LAST_POINT },                                                          // Right bracket
  [0x32] = { 0, 0, 0, 4, BR, BR, 6, 0, 6, 4, BR, BR, 0, 2, 6, 2, LAST_POINT },                              // I
  [0x33] = { 0, 0, 0, 6, BR, BR, 6, 0, 6, 6, BR, BR, 0, 1, 6, 1, BR, BR, 0, 4, 6, 4, LAST_POINT },          // II
  [0x34] = { 2, 0, 2, 5, BR, BR, 4, 0, 4, 5, LAST_POINT },                                                  // equals
  [0x35] = { 3, 0, 3, 5, LAST_POINT },                                                                      // dash
  [0x36] = { 0, 2, 2, 2, BR, BR, 4, 2, 6, 2, BR, BR, 0, 5, 2, 5, BR, BR, 4, 5, 6, 5 },                      // !!
  [0x37] = { 0, 2, 2, 2, BR, BR, 4, 2, 6, 2, BR, BR, 0, 5, 2, 5, BR, BR, 4, 5, 6, 5 },                      // !! different style
  [0x38] = { 0, 3, 2, 3, BR, BR, 4, 3, 6, 3 },                                                              // !
  [0x39] = { 0, 3, 2, 3, BR, BR, 4, 3, 6, 3 },                                                              // ! different style
  [0x3A] = { 3, 0, 6, 0, LAST_POINT },                                                                      // '
  [0x3B] = { 3, 2, 6, 2, BR, BR, 4, 4, 6, 4, LAST_POINT },                                                  // "
  [0x3C] = { 3, 2, 6, 2, BR, BR, 4, 4, 6, 4, LAST_POINT },                                                  // "
  [0x3D] = { 3, 2, 6, 2, BR, BR, 4, 4, 6, 4, LAST_POINT },                                                  // " (should be skinny quote marks)
  [0x3E] = { 0, 0, 7, 0, 7, 7, LAST_POINT },                                                                // L shape (right, bottom)
  [0x3F] = { 7, 0, 7, 7, 0, 7, LAST_POINT },                                                                // L shape, (right, top)
  [0x40] = { 7, 0, 0, 0, 0, 7, LAST_POINT },                                                                // L shape
  [0x41] = { 0, 0, 7, 0, 7, 7, LAST_POINT },                                                                // L shape, (left, top)
  [0x42] = { 2, 2, LAST_POINT },                                                                            // 42 is dot
  [0x43] = { 2, 2, 0, 0, LAST_POINT },                                                                      // 43 is comma
  [0x44] = { 0, 5, 4, 5, 4, 7, 2, 7, 0, 8, BR, BR, 2, 5, 2, 7, BR, BR, 4, 10, 1, 10, 0, 11, 0, 12, 1, 13, 4, 13, BR,
             BR, 0, 15, 4, 15, 4, 17, 2, 17, 2, 18, 0, 18, 0, 15, BR, BR, 2, 15, 2, 17, BR, BR, 0, 23,
             0, 21, 4, 21, 4, 23, BR, BR, 2, 21, 2, 22, BR, BR, 0, 25, 4, 25, 0, 28, 4, 28, BR, BR, 0,
             30, 4, 30, 4, 32, 3, 33, 1, 33, 0, 32, 0, 30, LAST_POINT },  // 44 - 48 RUB END graphic
  [0x45] = { LAST_POINT },
  [0x46] = { LAST_POINT },
  [0x47] = { LAST_POINT },
  [0x48] = { LAST_POINT },
  [0x49] = { 0, 4, 2, 2, 5, 2, 7, 4, 7, 8, 5, 10, 2, 10, 0, 8, 0, 4, BR, BR, 2, 7, 2, 5, 5, 5, 5, 7, LAST_POINT },
  [0x4a] = { LAST_POINT },  // 4A copyright logo
  [0x4b] = { LAST_POINT },  // 4B, 4C = some logo?
  [0x4c] = { LAST_POINT },
  // 4D, - 4F = solid blocks of various colors
  [0x4D] = { BR, RED, 0, 0, 0, 7, 7, 7, 7, 0, 0, 0, LAST_POINT },  // attempt at a solid block (empty square for vector)
  [0x4E] = { BR, GRN, 0, 0, 0, 7, 7, 7, 7, 0, 0, 0, LAST_POINT },  // attempt at a solid block (empty square for vector)
  [0x4F] = { BR, BLU, 0, 0, 0, 7, 7, 7, 7, 0, 0, 0, LAST_POINT },  // attempt at a solid block (empty square for vector)
                                                                   // 50 = 67 = kong graphics
                                                                   //		["dk-front"]
  [0x50] = { 31, 20, 31, 17, 27, 13, 25, 13, 25, 15, 28, 15, 29, 16, 30, 18, 30, 19, 29, 20, BR, BR, 25, 20,
             25, 18, 24, 18, 24, 20, BR, BR, 21, 15, 22, 16, 22, 20, BR, BR, 26, 18, 27, 18, 27, 19, 26, 19,
             26, 18, BR, BR, 6, 20, 6, 16, 2, 12, BR, BR, 2, 4, 4, 4, 5, 3, 7, 3, 11, 7, 13, 7, 13, 4, 16, 1,
             19, 1, 23, 6, 24, 8, 24, 10, BR, BR, 7, 15, 8, 14, 10, 14, BR, BR, 19, 6, 17, 10, 16, 13, BR, BR,
             10, 13, 11, 10, BR, MBR, 27, 13, 27, 11, 26, 10, 25, 10, 21, 11, 20, 14, 19, 14, 18, 16, 18, 20,
             BR, BR, 2, 12, 0, 11, 0, 0, 2, 2, 2, 4, BR, BR, 16, 13, 16, 15, 15, 18, 14, 19, 12, 19, 10, 17,
             10, 13, BR, BR, 6, 17, 7, 17, 8, 16, BR, BR, 6, 19, 7, 19, 8, 18, BR, BR, 1, 10, 2, 11, BR, BR,
             1, 5, 2, 6, BR, BR, 28, 17, 28, 19, 26, 19, 26, 17, 28, 17, BR, LBR, 26, 18, 27, 18, 27, 19, 26, 19, 26, 18, LAST_POINT },

  /*  [0x50] = { BR, YEL, 5, 0, 7, 2, 7, 0, 5, 0, BR, RED, 2, 0, 2, 1, 1, 2, 0, 2, 0, 0, 2, 0, LAST_POINT },
  [0x51] = { BR, YEL, 0, 3, 2, 6, 7, 6, LAST_POINT },
  [0x52] = { BR, YEL, 0, 6, 7, 3, LAST_POINT },
  [0x53] = { BR, YEL, 0, 2, 1, 2, 3, 0, LAST_POINT },
  [0x54] = { 0, 6, 3, 0, 6, 6, 3, 0, 0, 0, 6, 0, LAST_POINT },  // letter K
  [0x55] = { 0, 6, 3, 0, 6, 6, 3, 0, 0, 0, 6, 0, LAST_POINT },  // letter K
  [0x56] = { 0, 6, 3, 0, 6, 6, 3, 0, 0, 0, 6, 0, LAST_POINT },  // letter K
  [0x57] = { 0, 6, 3, 0, 6, 6, 3, 0, 0, 0, 6, 0, LAST_POINT },  // letter K
  [0x58] = { 0, 6, 3, 0, 6, 6, 3, 0, 0, 0, 6, 0, LAST_POINT },  // letter K
  [0x59] = { 0, 6, 3, 0, 6, 6, 3, 0, 0, 0, 6, 0, LAST_POINT },  // letter K
  [0x5A] = { 0, 6, 3, 0, 6, 6, 3, 0, 0, 0, 6, 0, LAST_POINT },  // letter K
  [0x5B] = { 0, 6, 3, 0, 6, 6, 3, 0, 0, 0, 6, 0, LAST_POINT },  // letter K
  [0x5C] = { 0, 6, 3, 0, 6, 6, 3, 0, 0, 0, 6, 0, LAST_POINT },  // letter K
  [0x5D] = { 0, 6, 3, 0, 6, 6, 3, 0, 0, 0, 6, 0, LAST_POINT },  // letter K
  [0x5E] = { 0, 6, 3, 0, 6, 6, 3, 0, 0, 0, 6, 0, LAST_POINT },  // letter K
  [0x5F] = { 0, 6, 3, 0, 6, 6, 3, 0, 0, 0, 6, 0, LAST_POINT },  // letter K
  [0x60] = { 0, 6, 3, 0, 6, 6, 3, 0, 0, 0, 6, 0, LAST_POINT },  // letter K
  [0x61] = { 0, 6, 3, 0, 6, 6, 3, 0, 0, 0, 6, 0, LAST_POINT },  // letter K
  [0x62] = { 0, 6, 3, 0, 6, 6, 3, 0, 0, 0, 6, 0, LAST_POINT },  // letter K
  [0x63] = { 0, 6, 3, 0, 6, 6, 3, 0, 0, 0, 6, 0, LAST_POINT },  // letter K
  [0x64] = { 0, 6, 3, 0, 6, 6, 3, 0, 0, 0, 6, 0, LAST_POINT },  // letter K
  [0x65] = { BR, YEL, 0, 4, 4, 1, 7, 1, LAST_POINT },
  [0x66] = { BR, YEL, 0, 1, 7, 5, LAST_POINT },
  [0x67] = { BR, YEL, 0, 6, 3, 7, LAST_POINT },*/
  [0x68] = { LAST_POINT },
  [0x69] = { LAST_POINT },
  [0x6a] = { LAST_POINT },
  [0x6b] = { LAST_POINT },
  // 6C - 6F = BONUS graphic
  [0x6c] = { 2, 0, 2, 4, 3, 5, 4, 4, 5, 5, 6, 4, 6, 0, 2, 0, BR, BR, 4, 4, 4, 0, BR, BR, 3, 7, 2, 8, 2, 11, 3, 12, 5, 12, 6, 11, 6, 8, 5, 7, 3, 7, BR, BR, 2, 14, 6, 14, 2, 19, 6, 19, BR, BR, 6, 21, 3, 21, 2, 22, 2, 25, 3, 26, 6, 26, BR, BR, 2, 28, 2, 31, 4, 31, 4, 28, 5, 28, 6, 29, 6, 31, LAST_POINT },
  [0x6d] = { LAST_POINT },
  [0x6e] = { LAST_POINT },
  [0x6e] = { LAST_POINT },
  [0x6f] = { LAST_POINT },
  // 70-79 = 0 - 9 (larger, used in score and timer coloured red)
  [0x70] = { BR, RED, 0, 2, 0, 4, 2, 6, 4, 6, 6, 4, 6, 2, 4, 0, 2, 0, 0, 2, LAST_POINT },
  [0x71] = { BR, RED, 0, 0, 0, 6, BR, BR, 0, 3, 6, 3, 5, 1, LAST_POINT },
  [0x72] = { BR, RED, 0, 6, 0, 0, 5, 6, 6, 3, 5, 0, LAST_POINT },
  [0x73] = { BR, RED, 1, 0, 0, 1, 0, 5, 1, 6, 2, 6, 3, 5, 3, 2, 6, 6, 6, 1, LAST_POINT },
  [0x74] = { BR, RED, 0, 5, 6, 5, 2, 0, 2, 7, LAST_POINT },
  [0x75] = { BR, RED, 1, 0, 0, 1, 0, 5, 2, 6, 4, 5, 4, 0, 6, 0, 6, 5, LAST_POINT },
  [0x76] = { BR, RED, 3, 0, 1, 0, 0, 1, 0, 5, 1, 6, 2, 6, 3, 5, 3, 0, 6, 2, 6, 5, LAST_POINT },
  [0x77] = { BR, RED, 6, 0, 6, 6, 0, 2, LAST_POINT },
  [0x78] = { BR, RED, 2, 0, 0, 1, 0, 5, 2, 6, 5, 0, 6, 1, 6, 4, 5, 5, 2, 0, LAST_POINT },
  [0x79] = { BR, RED, 0, 1, 0, 4, 2, 6, 5, 6, 6, 5, 6, 1, 5, 0, 4, 0, 3, 1, 3, 6, LAST_POINT },
  // Lines for bonus box?
  [0x7a] = { LAST_POINT },
  [0x7b] = { LAST_POINT },

  /* [0x7c] = { 7, 0, 7, 8, BR, BR, 5, 8, 5, 0 },
  [0x7d] = { 0, 3, 7, 3, BR, BR, 7, 5, 0, 5 },
  [0x7e] = { LAST_POINT },
  [0x7f] = { 0, 3, 7, 3, BR, BR, 7, 5, 0, 5 }, */

  [0x7c] = { LAST_POINT },
  [0x7d] = { LAST_POINT },
  [0x7e] = { LAST_POINT },
  [0x7f] = { LAST_POINT },
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
